JHuinapi/Proyecto-biodise-o-13/Talleres/Luis Gutiérrez Núñez.pdf

Luis Gutierrez Nuñez

Introduction to Sketching

September 21, 2025

Luis Gutierrez Nuñez

Introduction to Part Studios

September 21, 2025

Luis Gutierrez Nuñez

September 21, 2025

Multi-Part Part Studios

Luis Gutierrez Nuñez

September 21, 2025

Onshape Assemblies

Luis Gutierrez Nuñez

September 21, 2025

Detailed Drawings
