JHuinapi/Proyecto-biodise-o-13/Talleres/Taller 8/jonatan-huinapi-dbc9e937-857c-474c-9bc4-7a5a633f69ce-certificate.pdf

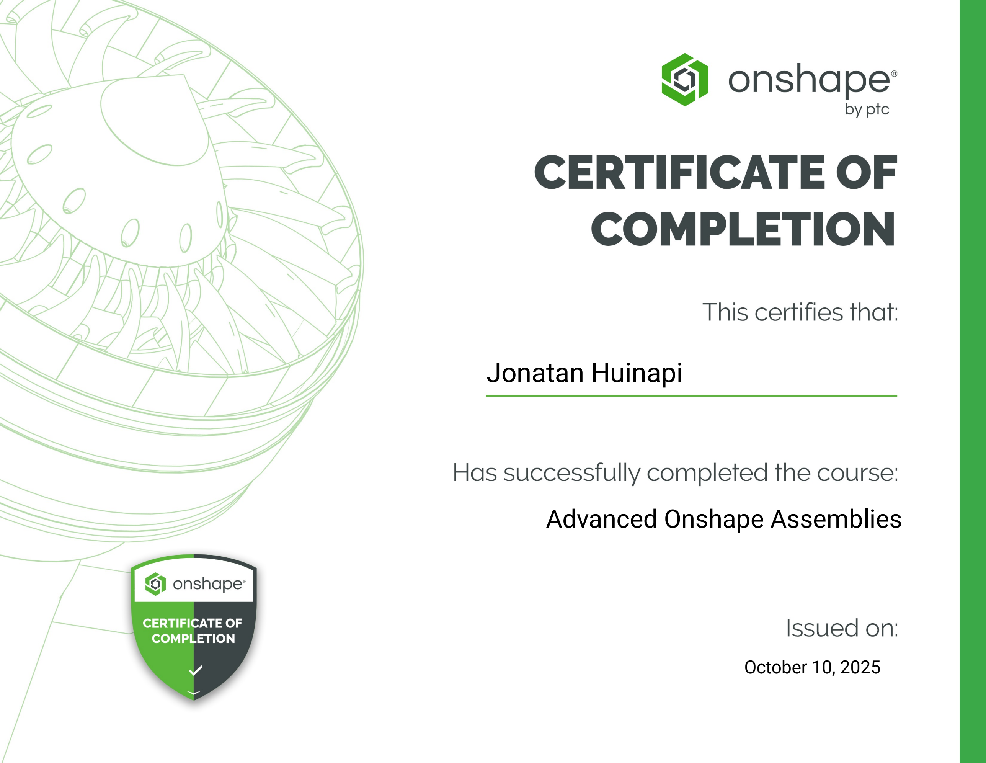
[picture p3: page 1]

Jonatan Huinapi

Advanced Onshape Assemblies

October 10, 2025
