JHuinapi/Proyecto-biodise-o-13/Documentacion/Entregables/Entregable N°8/Entregable N°8.pdf

## Entregable N°8

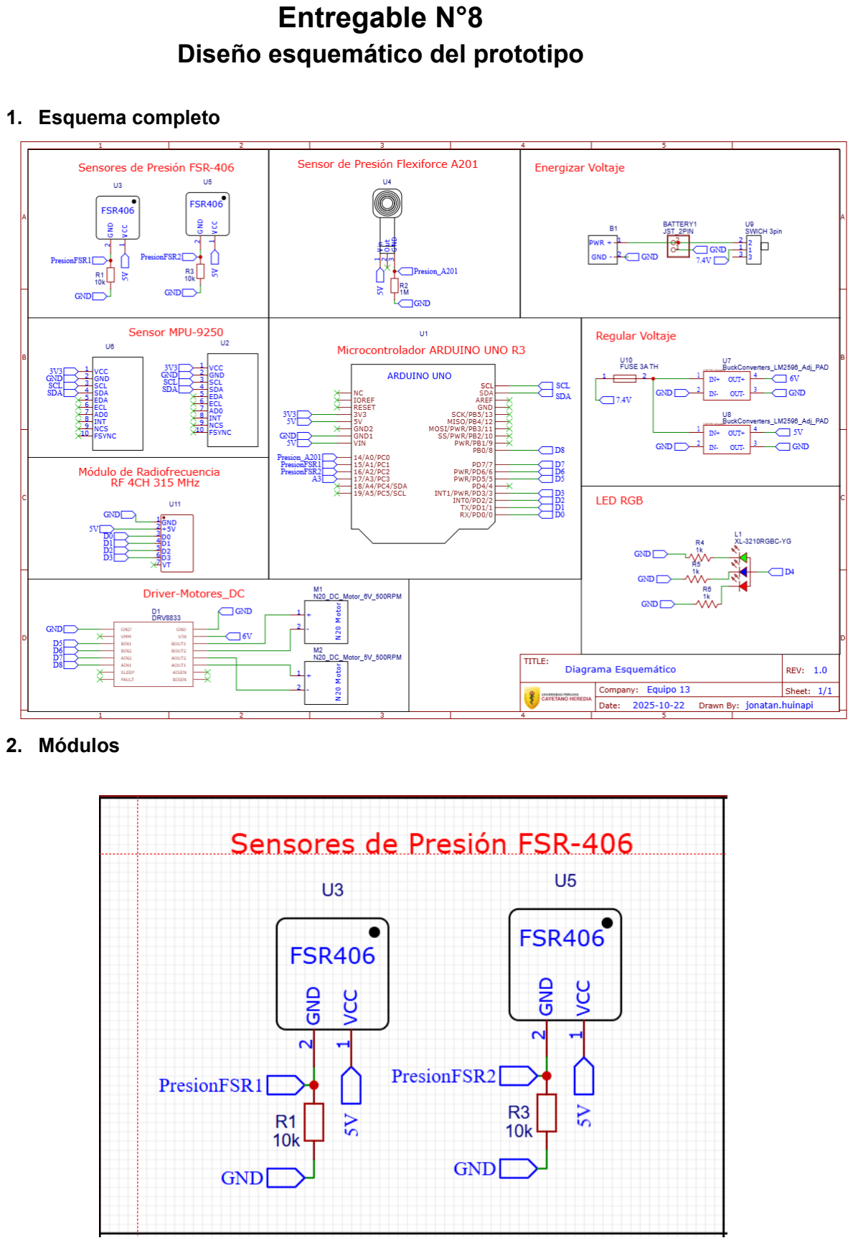
[picture p4: page 1]

### Diseño esquemático del prototipo

### 1. Esquema completo

### 2. Módulos

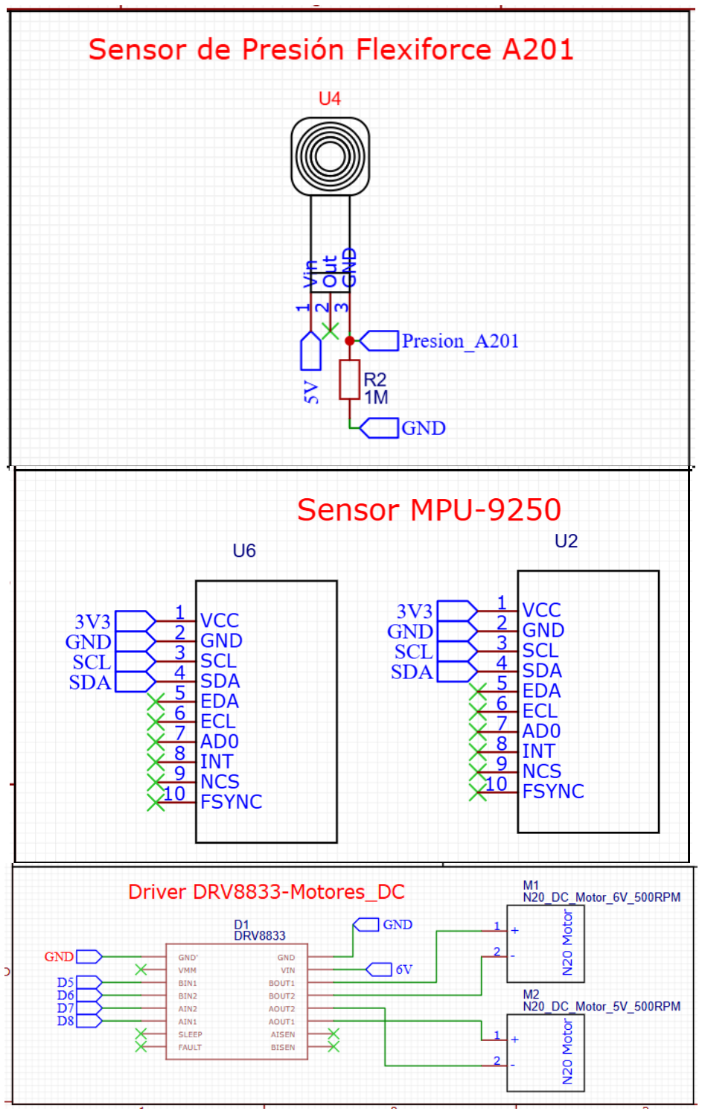
[picture p5: figure]
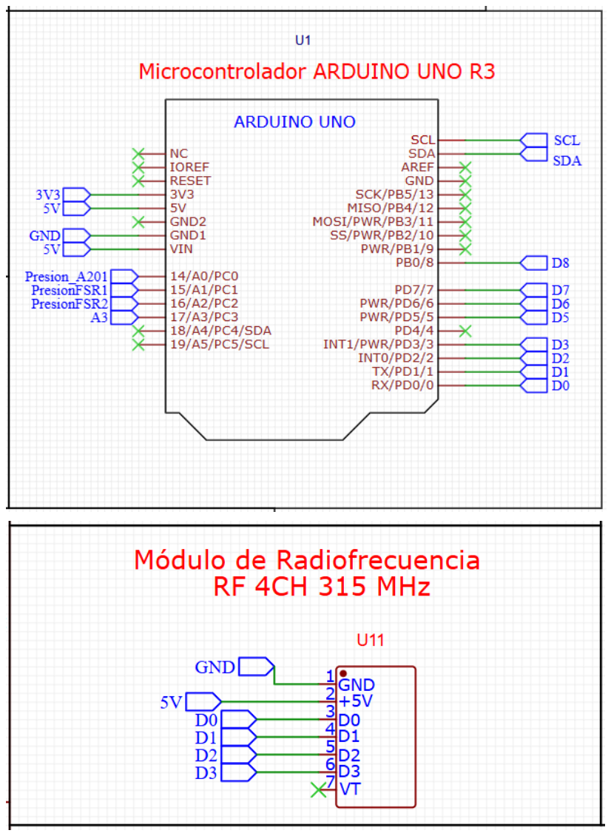
[picture p6: page 3]

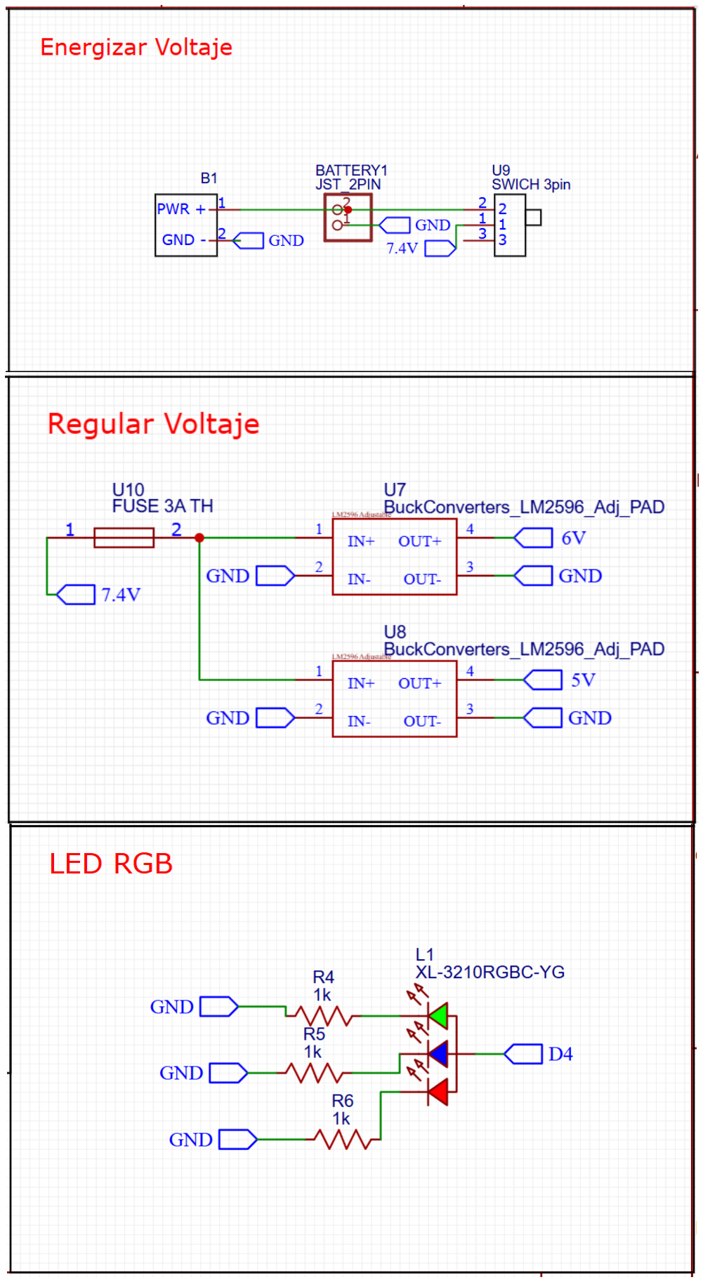
[picture p7: figure]

### Modelado 3D de los elementos que conforman su prototipo

Solución completa:
https://cad.onshape.com/documents/ef6f67d3207a1438bd075c8d/w/edfa028e2b72aa1350f10b2e/e/57896c7d0aa371fb77b32f57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 (https://cad.onshape.com/documents/ef6f67d3207a1438bd075c8d/w/edfa028e2b72aa1350f10b2e/e/57896c7d0aa371fb77b32f57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)

Componentes:

Arduino uno R3:

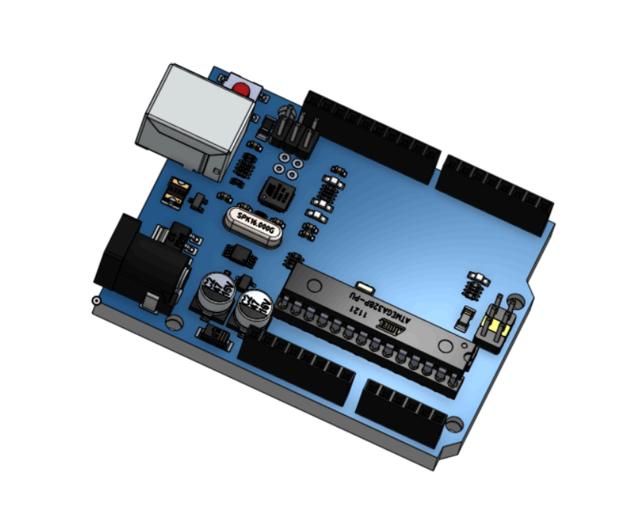
[picture p8: figure]

https://cad.onshape.com/documents/358e6ee0a7e545cdc13880cc/w/fb00525c6271bd48ed0 090b1 (https://cad.onshape.com/documents/358e6ee0a7e545cdc13880cc/w/fb00525c6271bd48ed0090b1)

LM 2596:

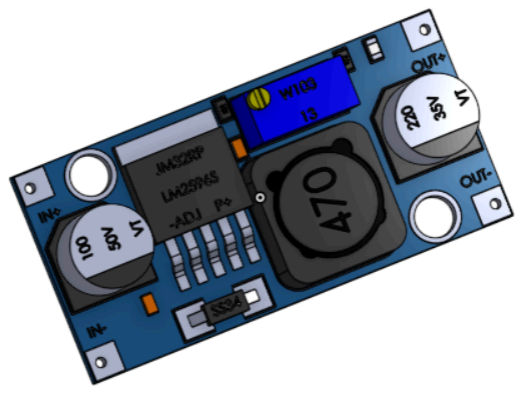
[picture p9: figure]

https://cad.onshape.com/documents/ed9dc76d7d66df3d99825e75/w/e64b5db6f0701456e918e3b2/e/382bef30aee71854fb0a7432 (https://cad.onshape.com/documents/ed9dc76d7d66df3d99825e75/w/e64b5db6f0701456e918e3b2/e/382bef30aee71854fb0a7432)

MPU 9250:

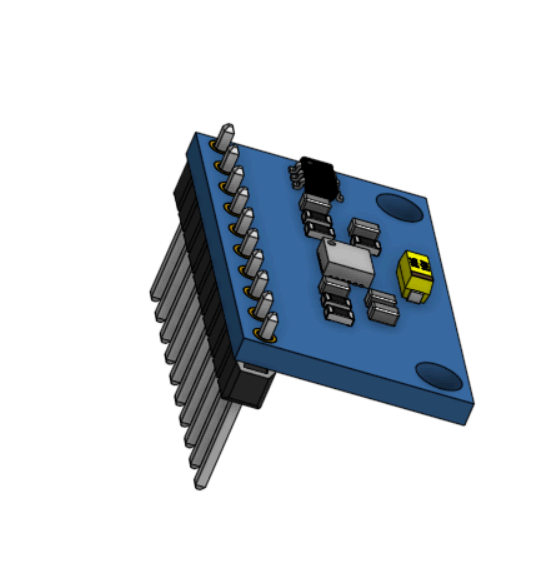
[picture p10: figure]

https://cad.onshape.com/documents/4e7dba8231ca7aadc371da44/w/675151ea96279376c8e2b919/e/e5ab18771fac6c1b0bbd111b (https://cad.onshape.com/documents/4e7dba8231ca7aadc371da44/w/675151ea96279376c8e2b919/e/e5ab18771fac6c1b0bbd111b)

Soporte largo:

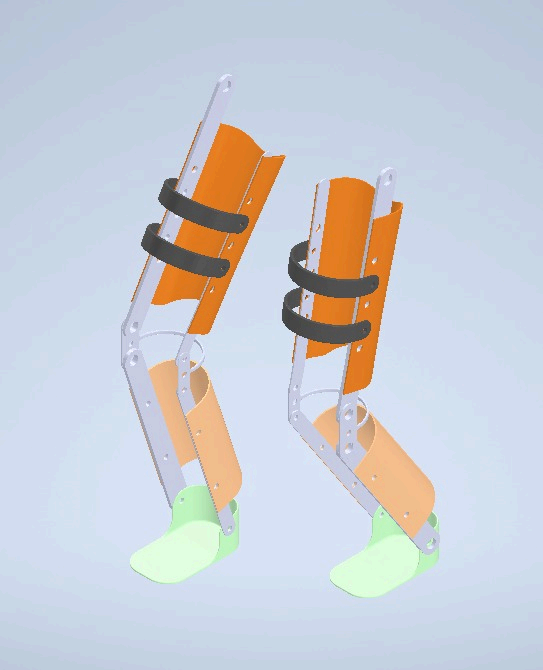
[picture p11: figure]

Ortesis para ambas piernas: https://cad.onshape.com/documents/b46cb4fec5818db489978633/w/90fc2fcc2cd690b41c06a4c6/e/ea05ce6ca1045edb00a44d7a (https://cad.onshape.com/documents/b46cb4fec5818db489978633/w/90fc2fcc2cd690b41c06a4c6/e/ea05ce6ca1045edb00a44d7a) https://cad.onshape.com/documents/85059d7c032bed2c8b1fd105/w/9daea419ead4c4d947 5dbce7 (https://cad.onshape.com/documents/85059d7c032bed2c8b1fd105/w/9daea419ead4c4d9475dbce7)

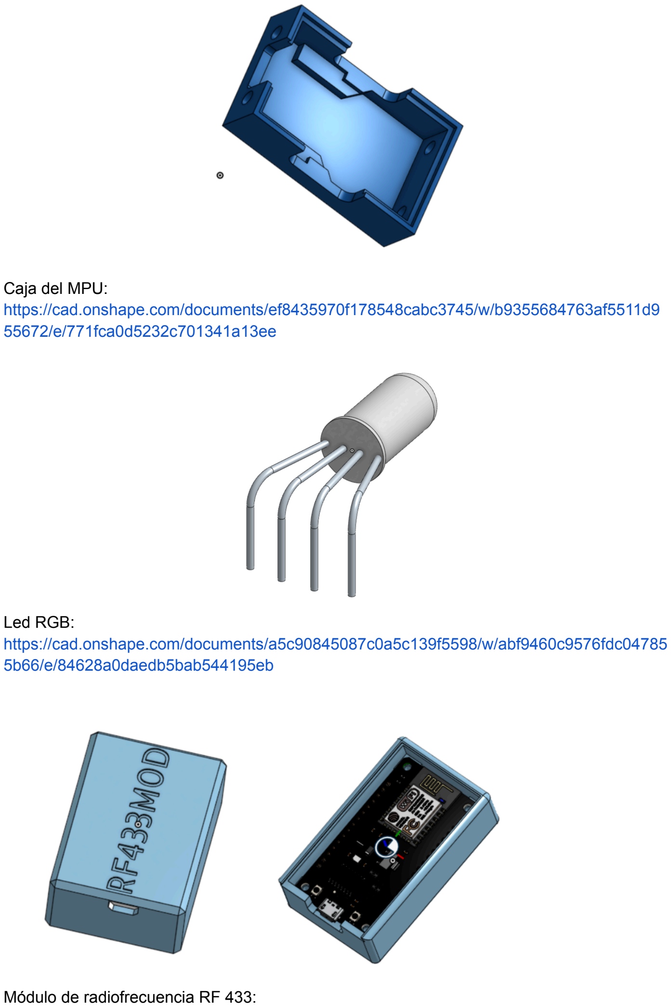
[picture p12: page 7]

Caja del MPU:
https://cad.onshape.com/documents/ef8435970f178548cabc3745/w/b9355684763af5511d955672/e/771fca0d5232c701341a13ee (https://cad.onshape.com/documents/ef8435970f178548cabc3745/w/b9355684763af5511d955672/e/771fca0d5232c701341a13ee)

Led RGB:
https://cad.onshape.com/documents/a5c90845087c0a5c139f5598/w/abf9460c9576fdc047855b66/e/84628a0daedb5bab544195eb (https://cad.onshape.com/documents/a5c90845087c0a5c139f5598/w/abf9460c9576fdc047855b66/e/84628a0daedb5bab544195eb)

Módulo de radiofrecuencia RF 433:

https://cad.onshape.com/documents/46bb01dfa372f61e05a1ae57/w/6816e948a11d4f39ffd87c3d/e/570a766bd7e573b261936c9a (https://cad.onshape.com/documents/46bb01dfa372f61e05a1ae57/w/6816e948a11d4f39ffd87c3d/e/570a766bd7e573b261936c9a) https://cad.onshape.com/documents/9d52821e4076e5f0773620d1/w/937a06b7c89ce3c964217ad0/e/10f29af23418c9318d54ea03 (https://cad.onshape.com/documents/9d52821e4076e5f0773620d1/w/937a06b7c89ce3c964217ad0/e/10f29af23418c9318d54ea03)

Parte del bastón canadiense:

Baston candiense:

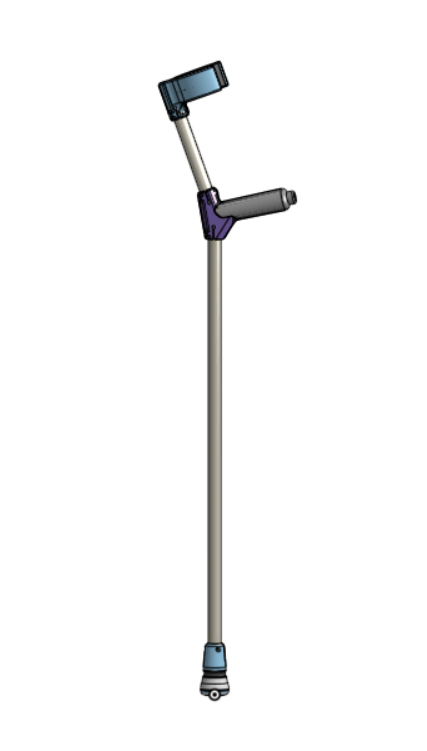
[picture p13: figure]

https://cad.onshape.com/documents/13cb7400194ab0a934fd1462/w/0d99d2ad3d134e4b89628924/e/30bec052ad2776449d337491 (https://cad.onshape.com/documents/13cb7400194ab0a934fd1462/w/0d99d2ad3d134e4b89628924/e/30bec052ad2776449d337491)

Soporte de boton:

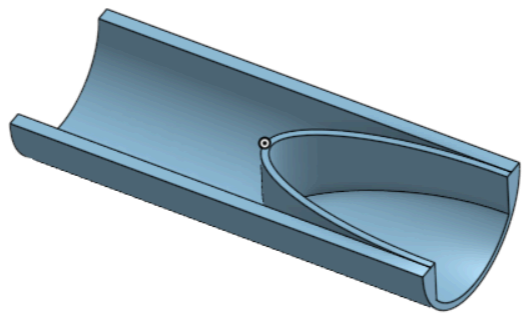
[picture p14: figure]

https://cad.onshape.com/documents/9404f07777c095b4e53f477f/w/989ea8cd8fd72e54b5d60ba9/e/30a6f88c9f77ebc46748e171 (https://cad.onshape.com/documents/9404f07777c095b4e53f477f/w/989ea8cd8fd72e54b5d60ba9/e/30a6f88c9f77ebc46748e171)

Bateria Lipo:

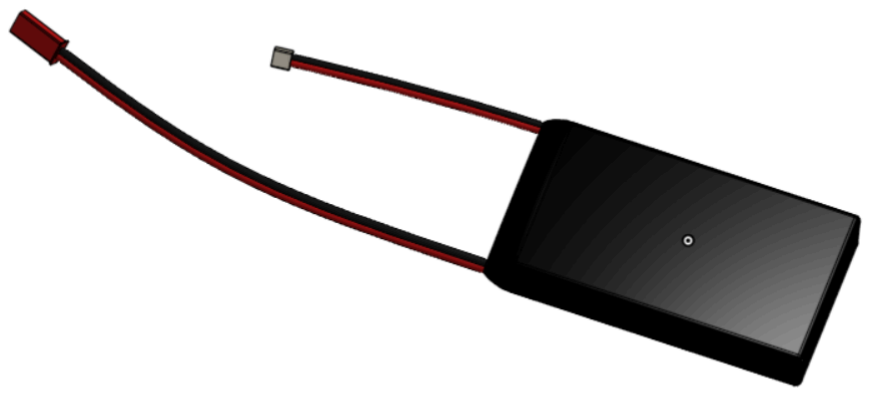
[picture p15: figure]

https://cad.onshape.com/documents/a1dde294c337bbebe96d0394/w/6668284372e06987ff7d8810/e/77b050f4c0bf37e111e226cb (https://cad.onshape.com/documents/a1dde294c337bbebe96d0394/w/6668284372e06987ff7d8810/e/77b050f4c0bf37e111e226cb)

Partes de la plantilla:

Plantilla:

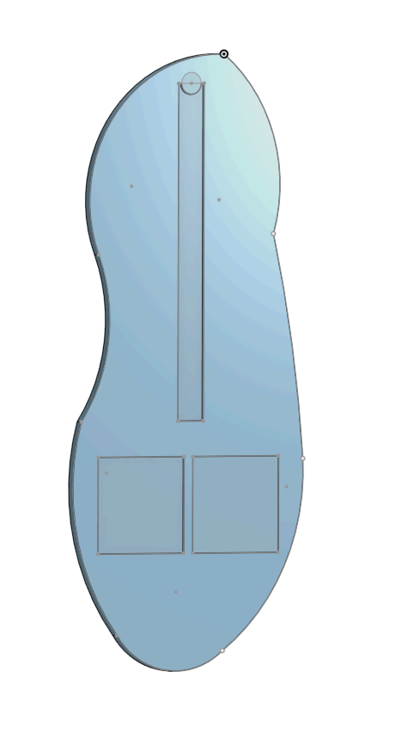
[picture p16: figure]

https://cad.onshape.com/documents/90b00f3962dbd41c6fcc8b45/w/5ce1db6625fad7db0d8d7604/e/39d914baed3868cf32210c26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 (https://cad.onshape.com/documents/90b00f3962dbd41c6fcc8b45/w/5ce1db6625fad7db0d8d7604/e/39d914baed3868cf32210c26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)

Sensores de fuerza:

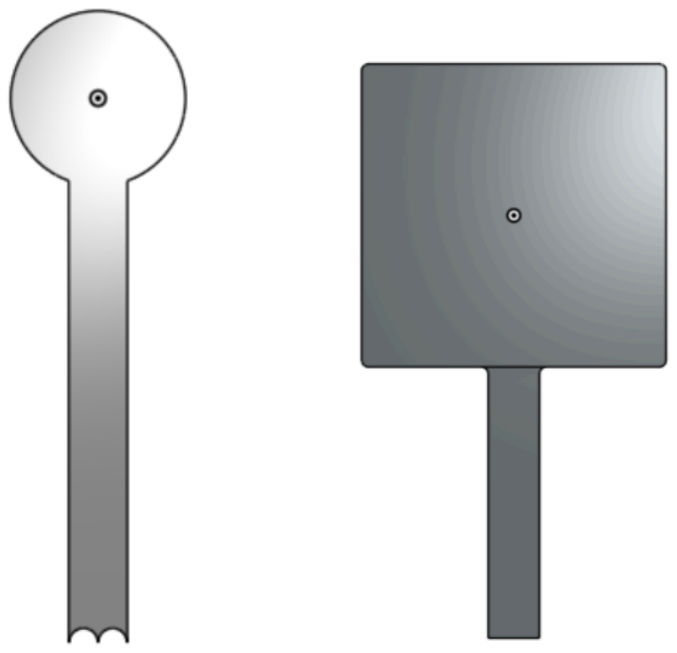
[picture p17: figure]

https://cad.onshape.com/documents/090143753a29e05ed30aaa47/w/a6cd4efa5bea32224642f22c/e/10581780c01f5d9f3ce7b4fe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 (https://cad.onshape.com/documents/090143753a29e05ed30aaa47/w/a6cd4efa5bea32224642f22c/e/10581780c01f5d9f3ce7b4fe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) https://cad.onshape.com/documents/b9766196f22d7fde754003f2/w/f4f8ca196eb82ef86cc7a587/e/8ac04a6db70dde7c7fe50fd8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 (https://cad.onshape.com/documents/b9766196f22d7fde754003f2/w/f4f8ca196eb82ef86cc7a587/e/8ac04a6db70dde7c7fe50fd8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)

Partes del sistema de trabe y destrabe:

Micromotor N20:

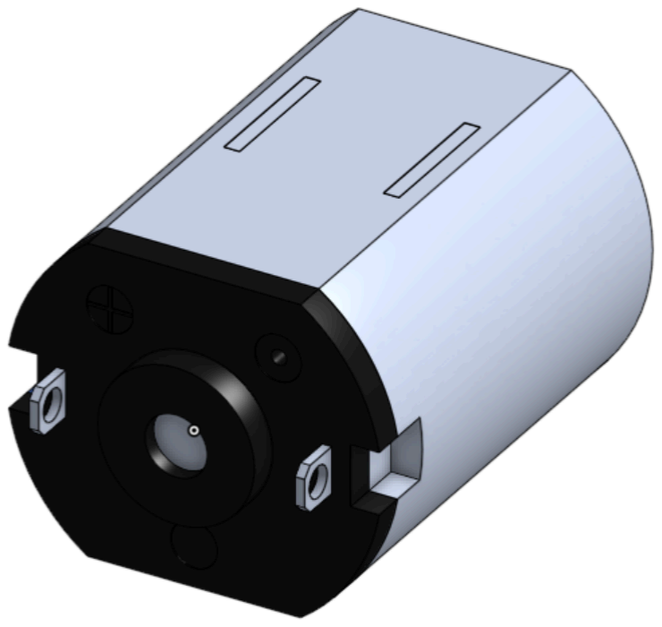
[picture p18: figure]

https://cad.onshape.com/documents/a79e828ba8c9972a8f85b02b/w/044c2e34d4fcb483626a1345/e/9966f7c9ecc495e53f5c1f4e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 (https://cad.onshape.com/documents/a79e828ba8c9972a8f85b02b/w/044c2e34d4fcb483626a1345/e/9966f7c9ecc495e53f5c1f4e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)

Poleas:

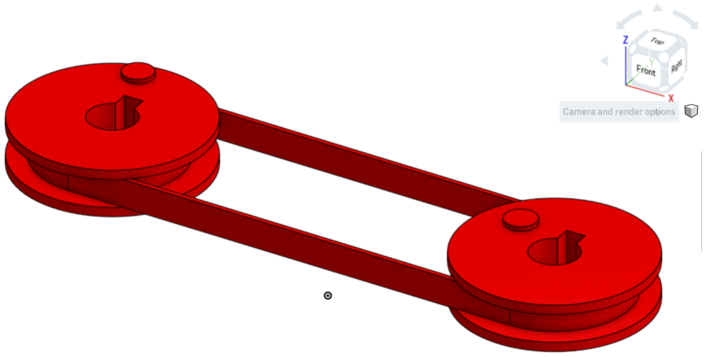
[picture p19: figure]

https://cad.onshape.com/documents/feb36c91eed124813346efae/w/b8817322451c90e2da5b96ee/e/90c357cbd19b11150c3f9f70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 (https://cad.onshape.com/documents/feb36c91eed124813346efae/w/b8817322451c90e2da5b96ee/e/90c357cbd19b11150c3f9f70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)

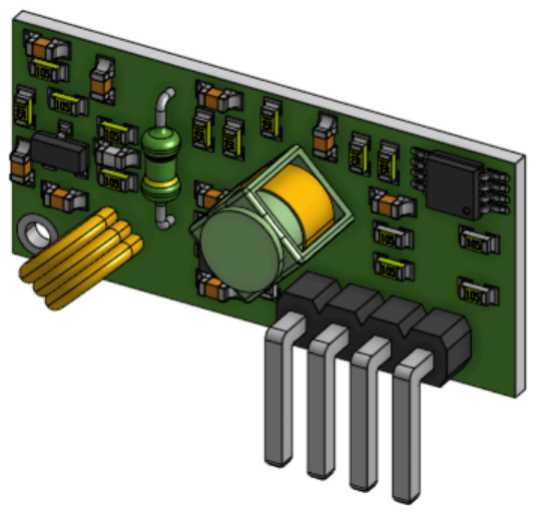
[picture p20: figure]

01COM RX RF433 Receiver:
https://cad.onshape.com/documents/082a6ee97619ae0f739f296e/w/c65dcdce71237949594d5020/e/2d733671bed38224296ad423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 2 (https://cad.onshape.com/documents/082a6ee97619ae0f739f296e/w/c65dcdce71237949594d5020/e/2d733671bed38224296ad423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)

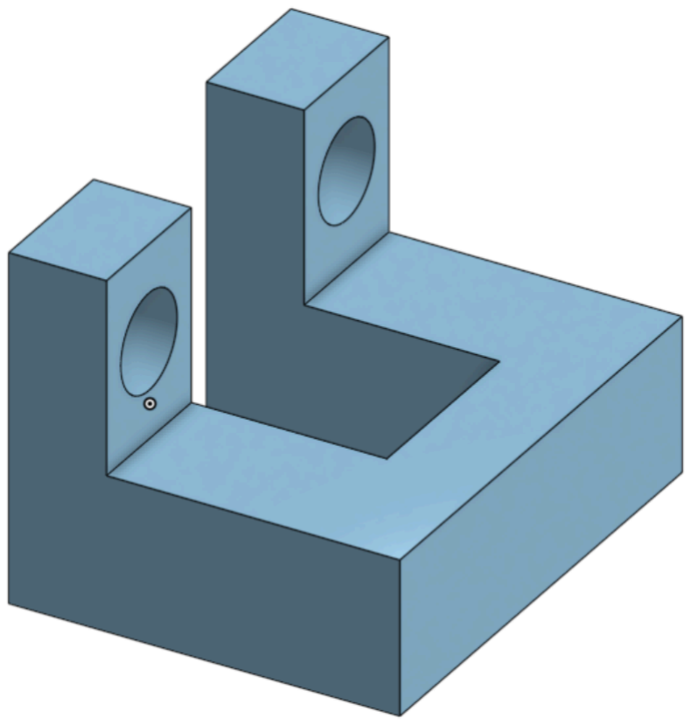
[picture p21: figure]

Gancho para poleas:
https://cad.onshape.com/documents/0540d481ef109f192a8d81a9/w/1a57b690e35bc69c4da5a976/e/339e8275e2c3247a0a6f577b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 (https://cad.onshape.com/documents/0540d481ef109f192a8d81a9/w/1a57b690e35bc69c4da5a976/e/339e8275e2c3247a0a6f577b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)

Pieza para trabar:

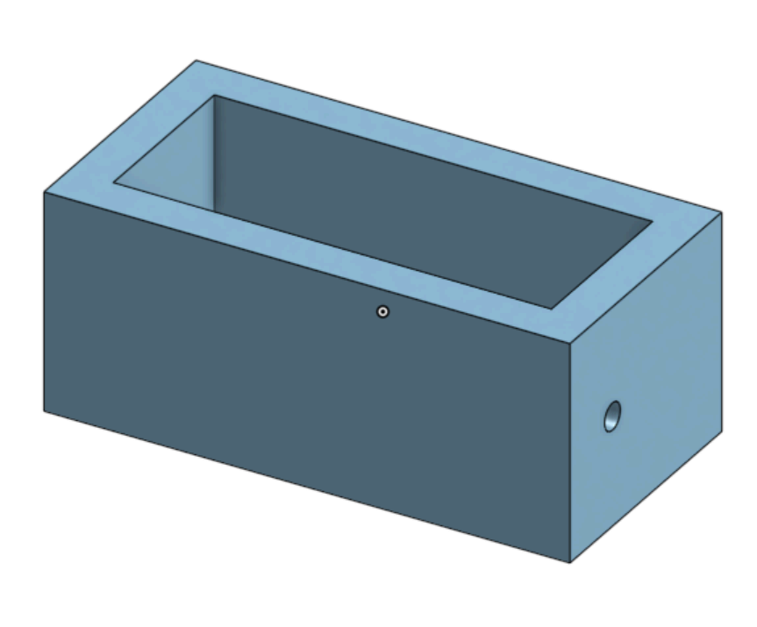
[picture p22: figure]

https://cad.onshape.com/documents/76d2d7c239bdc8f8fa00e4ad/w/cebd49e91c2a0bf198104d18/e/7dd4c7551fcfe9fa7b047bc8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 (https://cad.onshape.com/documents/76d2d7c239bdc8f8fa00e4ad/w/cebd49e91c2a0bf198104d18/e/7dd4c7551fcfe9fa7b047bc8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)
