JHuinapi/Proyecto-biodise-o-13/Documentacion/Hito №2/Hito 2_FdB_2025_2.pdf

## Indicaciones

- Este template es un esquema base para la construcción de su Elevator Pitch en base a los entregables del curso.
- Se recomienda hacer una presentación con alto contenido visual, enfocada en presentar ideas centrales en un Pitch de 7 minutos.
- El diseño estético de la carátula y de las demás diapositivas queda a criterio del alumno. El orden y contenido indicado en cada slide es obligatorio.
- Se recomienda ceñirse al número de slides del template, para utilizar aproximadamente 1 min/diapositiva y culminar en el tiempo asignado. Sean precisos y claros en su discurso.
- El slide para la demo está fuera de los 7 min y puede durar 2:00 min máx. Los slides extra son para información de soporte durante las preguntas de los asesores respecto a los retos y limitaciones de sus prototipos.
- Asistir con vestimenta formal para la presentación del Hito N° 2.

¡Éxitos en su presentación!

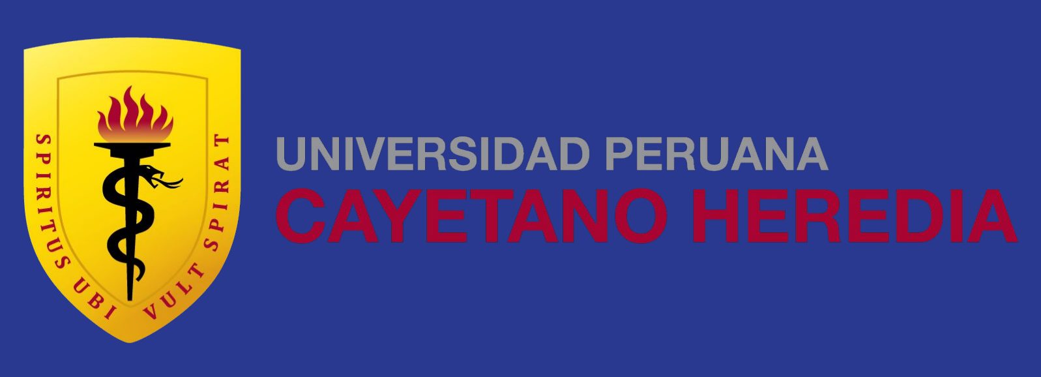
[picture p49: figure]

# KAFO-Pulley Assist

Integrantes: Grupo 13

- Gutierrez Nuñez, Luis Antonio. Rol: Técnico en electrónica y programación
- Hernandez Jeronimo, Xavier Alexis. Rol: Responsable de metodología y documentación
- Huiñapi Huaman, Jonatan Esteban. Rol: Líder del proyecto y especialista en electrónica y programación
- Mamani Casas, Alexandra Milagros. Rol: Diseñadora 3D principal
- Morocho Bustamante, Mariam Michelle. Rol: Diseñadora 3D y encargada de manufactura aditiva
- Murillo Sedano, Ricardo Sebastián. Rol: Apoyo metodológico y encargado de impresión 3D

## Problemática

- “ Control Method for a powered knee ankle foot orthosis”
- Número de patente: W02022231566
- Trainer in a pocket - proof-of-concept of mobile, real-time, foot kinematics feedback for gait pattern normalization in individuals after stroke, incomplete spinal cord injury and elderly patients
- Design, Control, and Pilot Study of a Lightweight and Modular Robotic Exoskeleton for Walking Assistance After Spinal Cord Injury

El paciente presenta una zona de preservación parcial (ZPP) en la rodilla, permitiendo su flexión. Además de la falta de sensibilidad en la parte inferior del cuerpo desde el nivel T10.

Referencias con mayor relevancia en el desarrollo del proyecto:

## Solución

Ortesis KAFO con bloqueo controlado mediante sistema de poleas motorizado.

Funcionamiento en tres pasos del prototipo:

1. El usuario presiona un botón para bloquear o desbloquear la rodilla.
2. Un motor acciona las poleas que mueven el mecanismo de drop lock, además se registran datos de posicionamiento del pie.
3. El sistema fija o libera la articulación según la orden enviada y brinda una retroalimentación de datos en forma de guía visual.

## Tracción

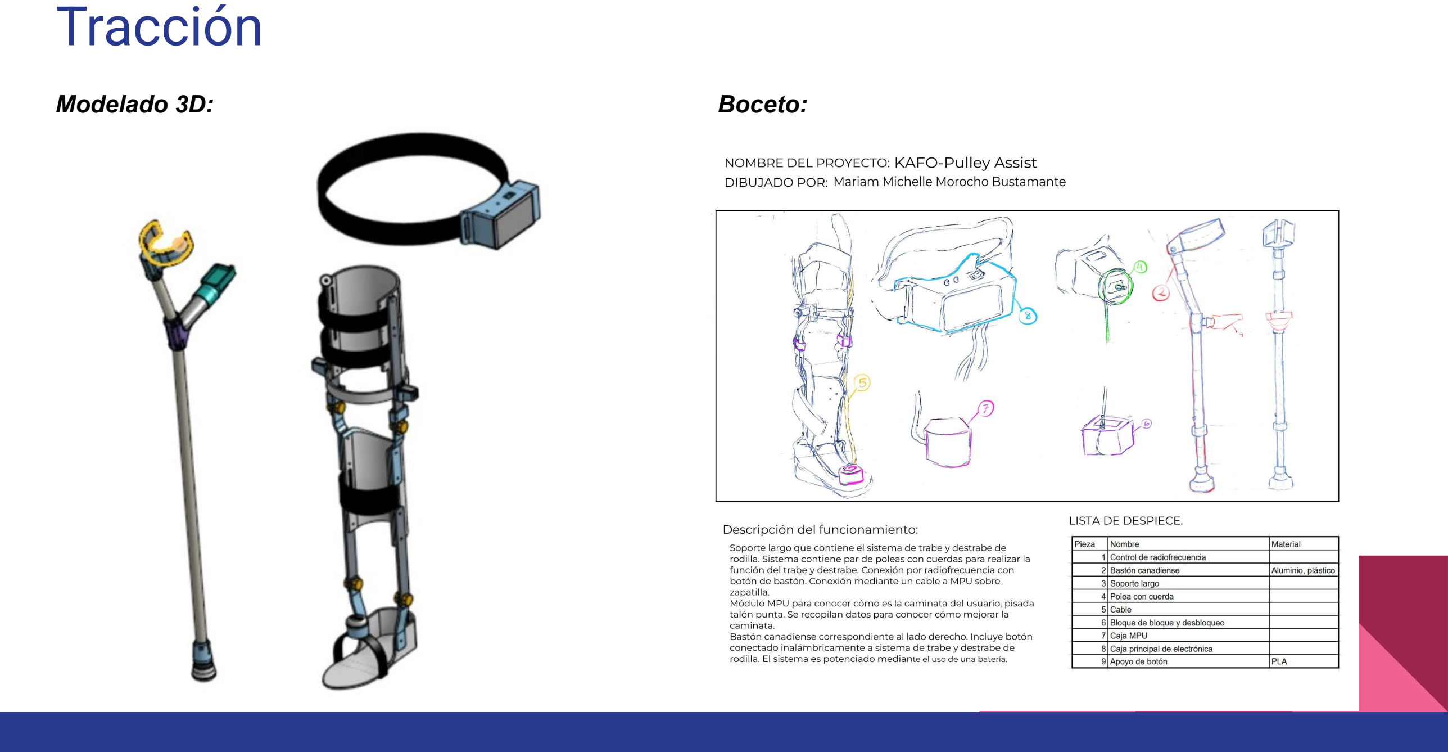
[picture p50: page 5]

Modelado 3D: | Boceto:

## Tracción

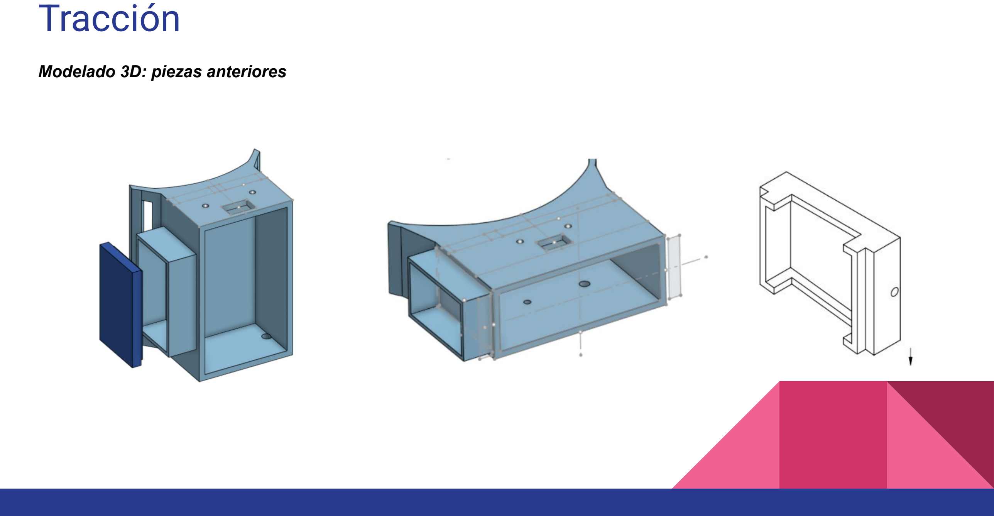
[picture p51: page 6]

Modelado 3D: piezas anteriores

## Tracción

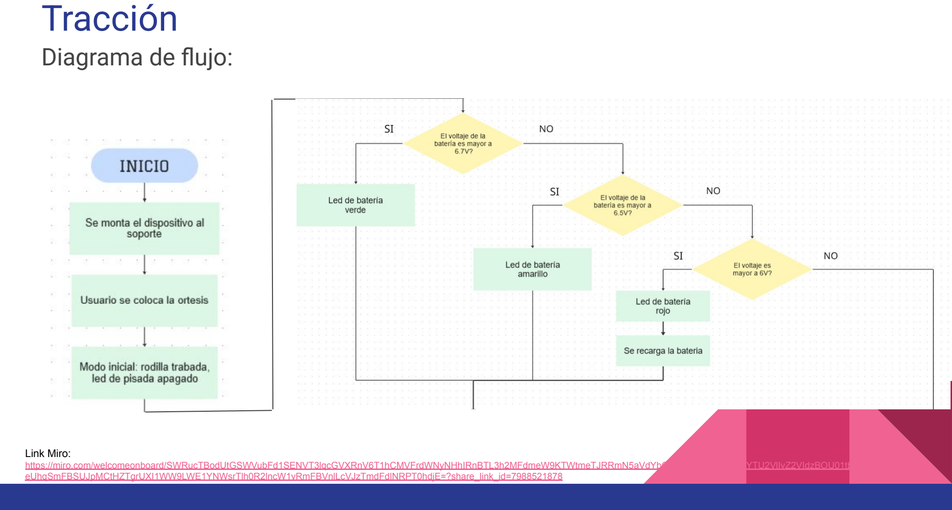
[picture p52: page 7]

Diagrama de flujo:

Link Miro:
https://miro.com/welcomeonboard/SWRucTBodUtGSWVubFd1SENVT3lqcGVXRnV6T1hCMVFrdWNyNHhIRnBTL3h2MFdmeW9KTWtmeTJRRmN5aVdYbGxjRTZJUUhTZUFPYTU2VlIvZ2VIdzBOU01tbndGR1pOQmM4e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 (https://miro.com/welcomeonboard/SWRucTBodUtGSWVubFd1SENVT3lqcGVXRnV6T1hCMVFrdWNyNHhIRnBTL3h2MFdmeW9KTWtmeTJRRmN5aVdYbGxjRTZJUUhTZUFPYTU2VlIvZ2VIdzBOU01tbndGR1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)

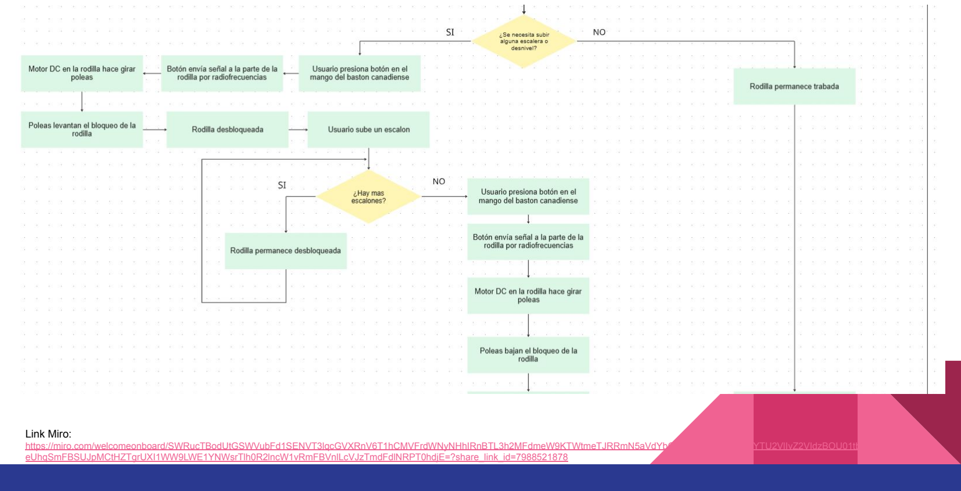
[picture p53: page 8]

Link Miro:
https://miro.com/welcomeonboard/SWRucTBodUtGSWVubFd1SENVT3lqcGVXRnV6T1hCMVFrdWNyNHhIRnBTL3h2MFdmeW9KTWtmeTJRRmN5aVdYbGxjRTZJUUhTZUFPYTU2VlIvZ2VIdzBOU01tbndGR1pOQmM4e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 (https://miro.com/welcomeonboard/SWRucTBodUtGSWVubFd1SENVT3lqcGVXRnV6T1hCMVFrdWNyNHhIRnBTL3h2MFdmeW9KTWtmeTJRRmN5aVdYbGxjRTZJUUhTZUFPYTU2VlIvZ2VIdzBOU01tbndGR1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)

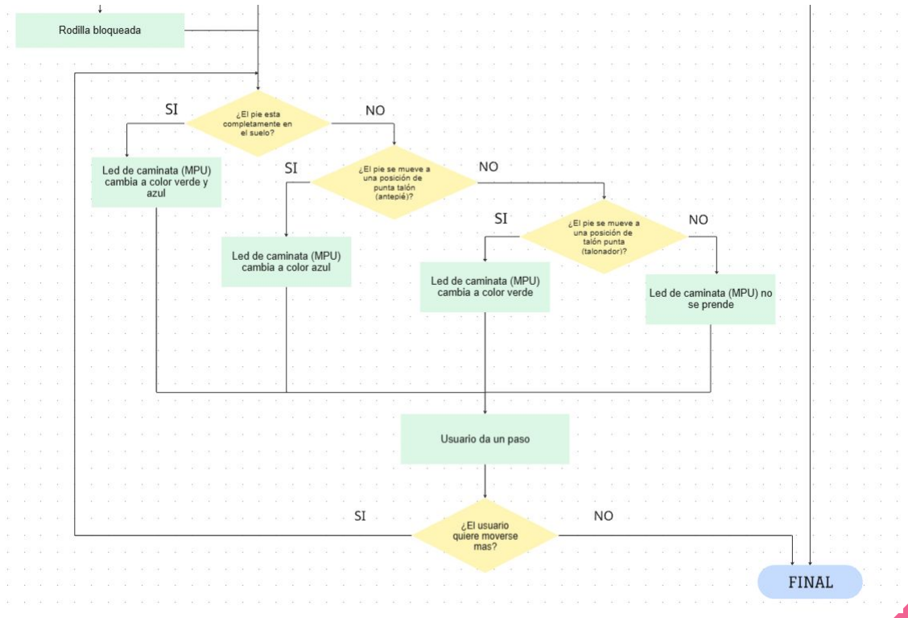
[picture p54: figure]

Link Miro:
https://miro.com/welcomeonboard/SWRucTBodUtGSWVubFd1SENVT3lqcGVXRnV6T1hCMVFrdWNyNHhIRnBTL3h2MFdmeW9KTWtmeTJRRmN5aVdYbGxjRTZJUUhTZUFPYTU2VlIvZ2VIdzBOU01tbndGR1pOQmM4e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 (https://miro.com/welcomeonboard/SWRucTBodUtGSWVubFd1SENVT3lqcGVXRnV6T1hCMVFrdWNyNHhIRnBTL3h2MFdmeW9KTWtmeTJRRmN5aVdYbGxjRTZJUUhTZUFPYTU2VlIvZ2VIdzBOU01tbndGR1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)

## Tracción

Entregable: Diagrama Esquemático del prototipo electrónico

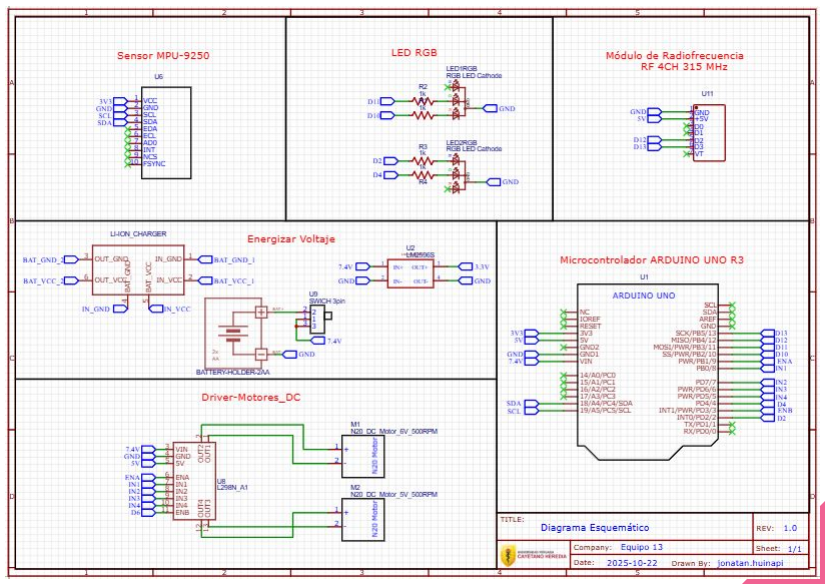
[picture p55: figure]

## Tracción

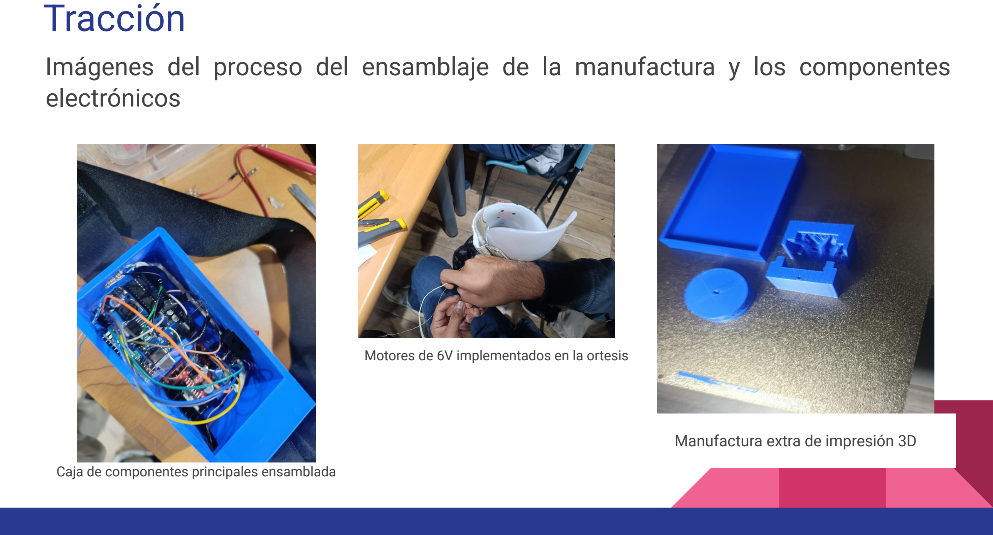
[picture p56: page 11]

Imágenes del proceso del ensamblaje de la manufactura y los componentes electrónicos

Caja de componentes principales ensamblada

Motores de 6V implementados en la ortesis

Manufactura extra de impresión 3D

## Tracción

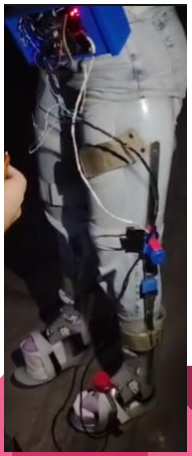
[picture p57: figure]

Resultados software: El dispositivo retroalimenta datos del estado de batería, además del correcto posicionamiento del pie y el usuario tiene acceso a los cambios de modo y encendido/apagado del sistema en general.

Resultados hardware: El dispositivo permite alternar entre modos sin apoyo de terceros, los componentes son acoplados de forma no invasiva a la ortesis y usuario, los elementos adicionales pesan menos de 600 gramos y no se presentan inconvenientes en la comodidad del usuario.

## Tracción: Demo

Videos del prototipo de baja fidelidad en ambas partes principales del proyecto

Funcionamiento mecánico | Funcionamiento electrónico

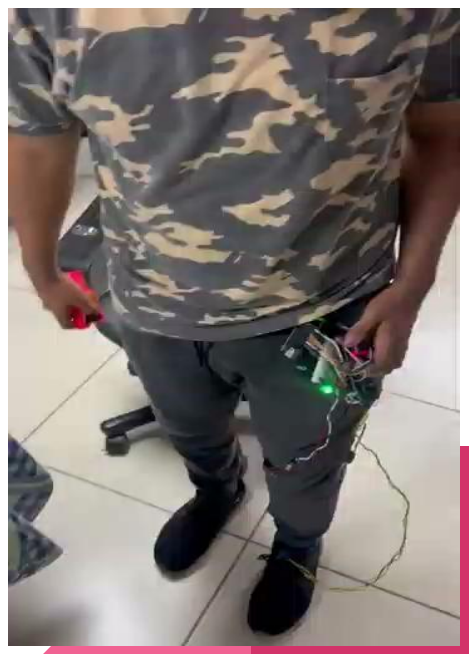
[picture p58: figure]

## Slide extra: Limitaciones

Se presentaron limitaciones externas tales como el cambio de material base el cual se cambió la forma y posicionamiento del soporte empleado en la ortesis. Para mitigar se tuvo que redimensionar el diseño entero.

Hubo limitaciones de tiempo en el trabajo debido al replanteamiento de idea por el sistema de reeducación implementado, además de el cambio de un modo de sistema automático a uno netamente semiautomático. Para mitigar se tuvo que mantener el mismo esquema de funciones y planteamiento de distribución de componentes cambiando algunos parámetros, pero manteniendo la idea general.

## Slide extra: Pruebas y testeos

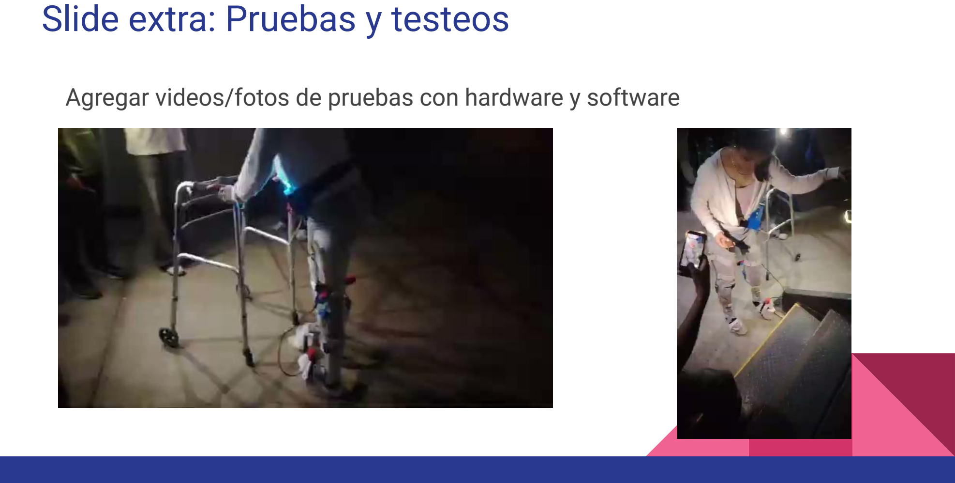
[picture p59: page 15]

Agregar videos/fotos de pruebas con hardware y software
