JHuinapi/Proyecto-biodise-o-13/Talleres/Jonatan Esteban Huiñapi Huaman/jonatan-huinapi-certificate-Introduction to sketching.pdf

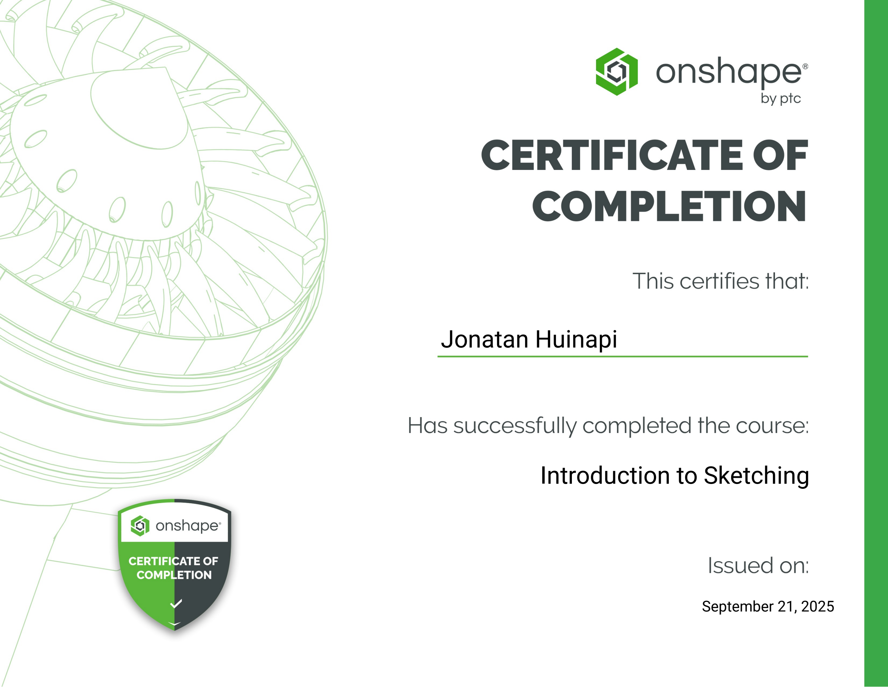
[picture p74: page 1]

Jonatan Huinapi

Introduction to Sketching

September 21, 2025
