JHuinapi/Proyecto-biodise-o-13/Talleres/Jonatan Esteban Huiñapi Huaman/jonatan-huinapi-Detailed Drawing-certificate.pdf

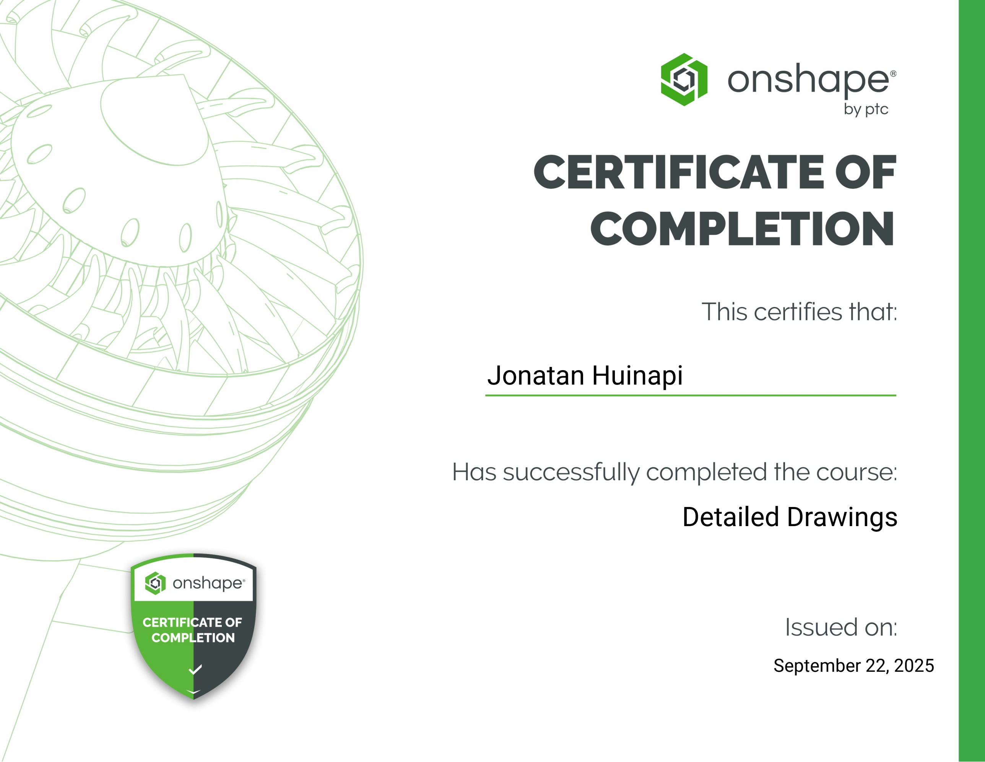
[picture p75: page 1]

Jonatan Huinapi

September 22, 2025

Detailed Drawings
