JHuinapi/Proyecto-biodise-o-13/Talleres/Jonatan Esteban Huiñapi Huaman/jonatan-huinapi-Introduction to part studios certificate.pdf

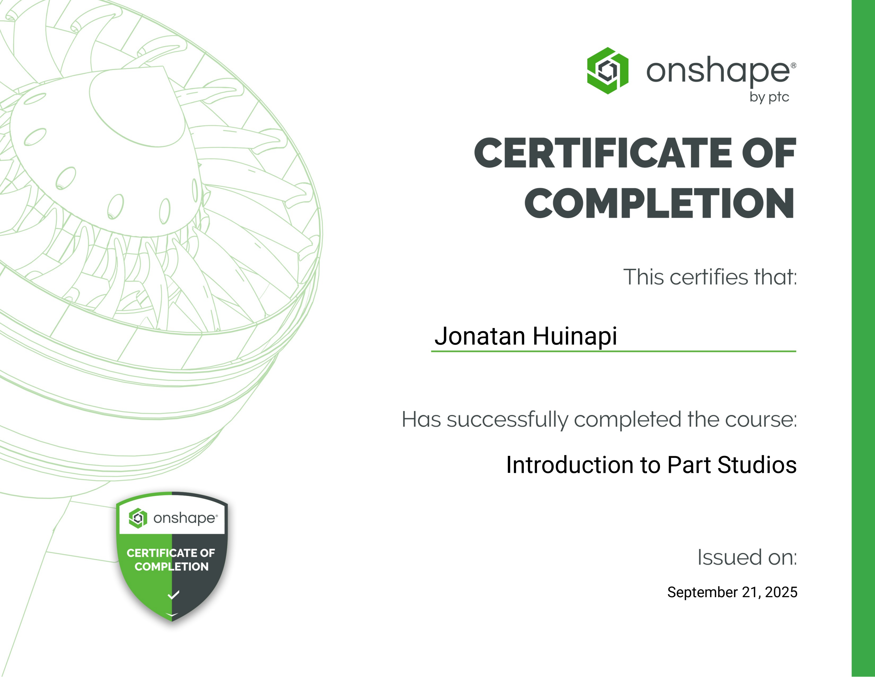
[picture p76: page 1]

Jonatan Huinapi

Introduction to Part Studios

September 21, 2025
