JHuinapi/Proyecto-biodise-o-13/Talleres/Jonatan Esteban Huiñapi Huaman/jonatan-huinapi-Multi-part Part studios-certificate.pdf

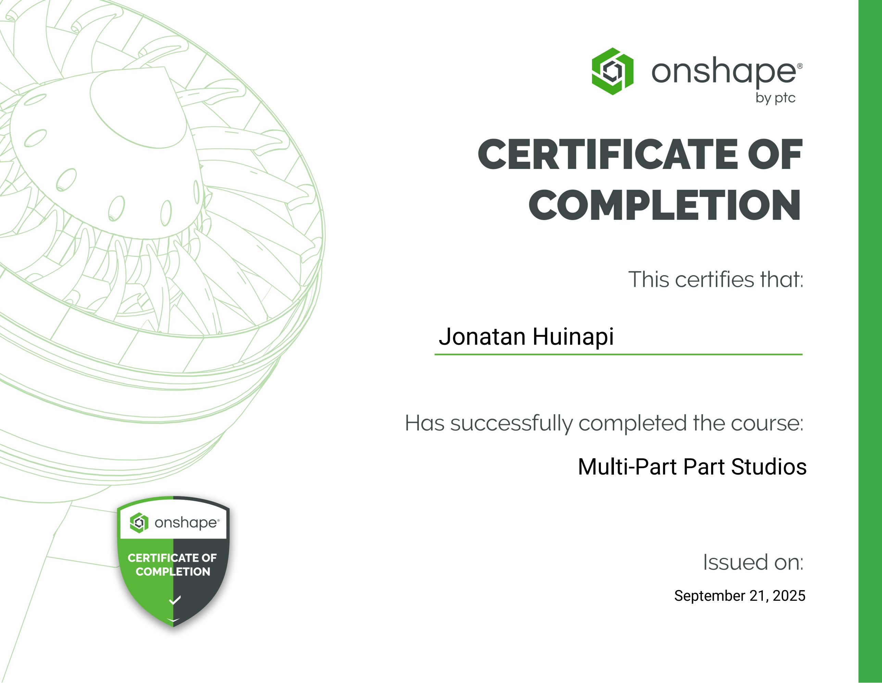
[picture p77: page 1]

Jonatan Huinapi

September 21, 2025

Multi-Part Part Studios
