JHuinapi/Proyecto-biodise-o-13/Talleres/Hernandez Jeronimo Xavier Alexis/Detailed Drawings.pdf

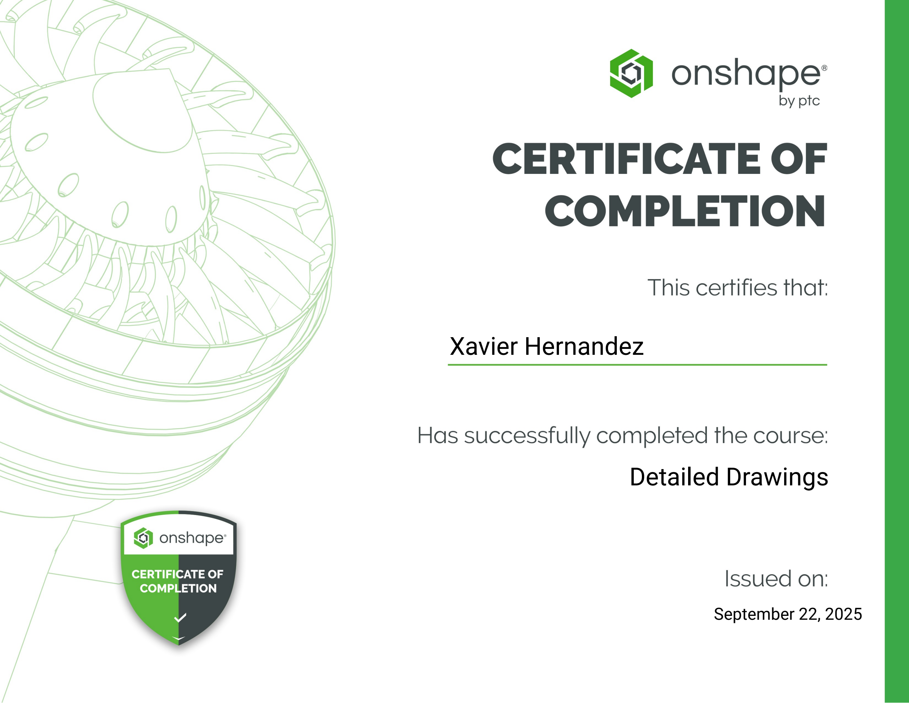
[picture p78: page 1]

Xavier Hernandez

September 22, 2025

Detailed Drawings
