JHuinapi/Proyecto-biodise-o-13/Talleres/Hernandez Jeronimo Xavier Alexis/Introduction to Part Studios.pdf

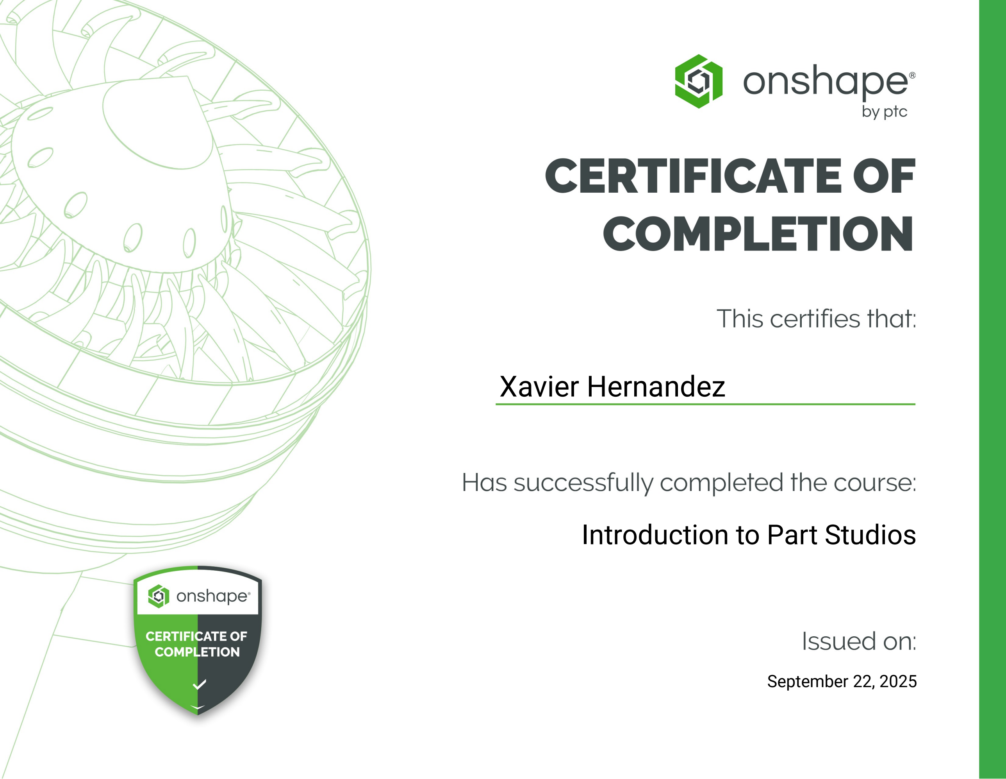
[picture p79: page 1]

Xavier Hernandez

Introduction to Part Studios

September 22, 2025
