JHuinapi/Proyecto-biodise-o-13/Talleres/Hernandez Jeronimo Xavier Alexis/Multi-Part Part Studios.pdf

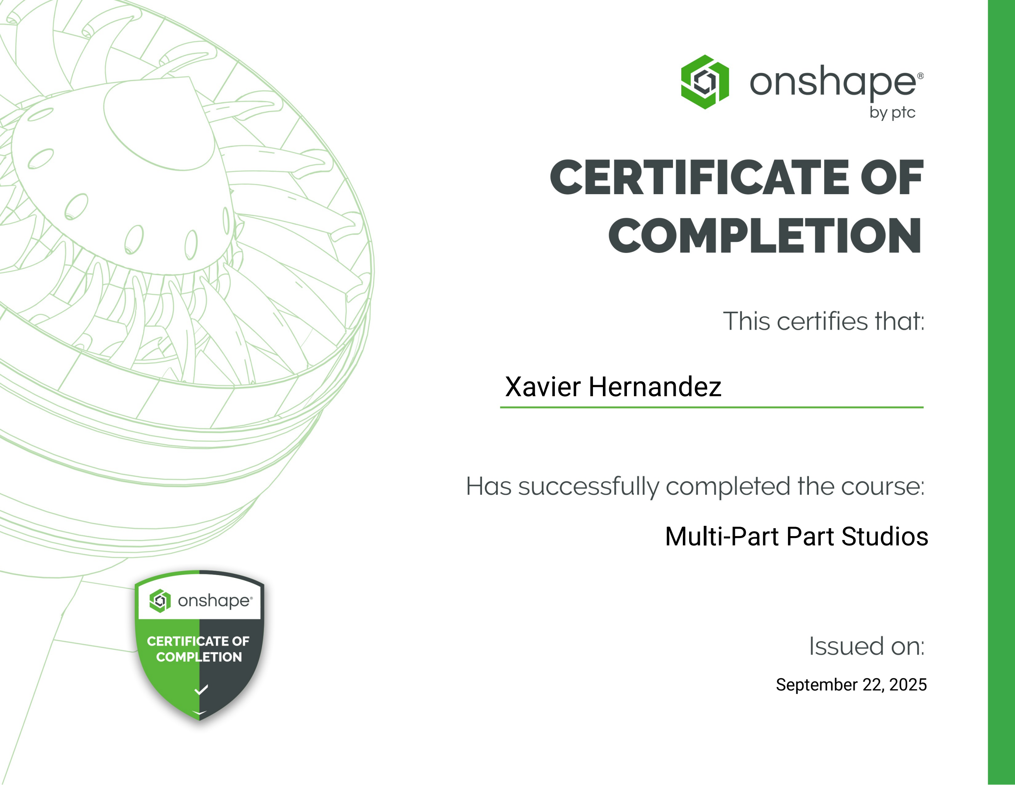
[picture p80: page 1]

Xavier Hernandez

September 22, 2025

Multi-Part Part Studios
