JHuinapi/Proyecto-biodise-o-13/Talleres/Hernandez Jeronimo Xavier Alexis/Introduction to Sketching.pdf

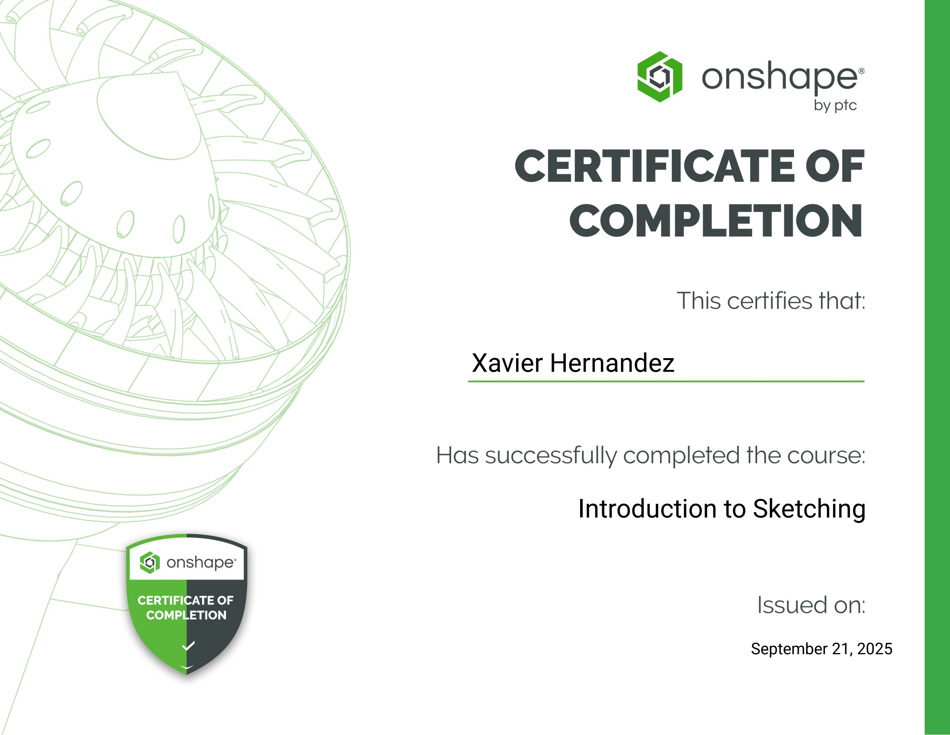
[picture p81: page 1]

Xavier Hernandez

Introduction to Sketching

September 21, 2025
