JHuinapi/Proyecto-biodise-o-13/Talleres/Morocho Bustamante, Mariam Michelle/MariamMorochoBustamante_DetailedDrawings.pdf

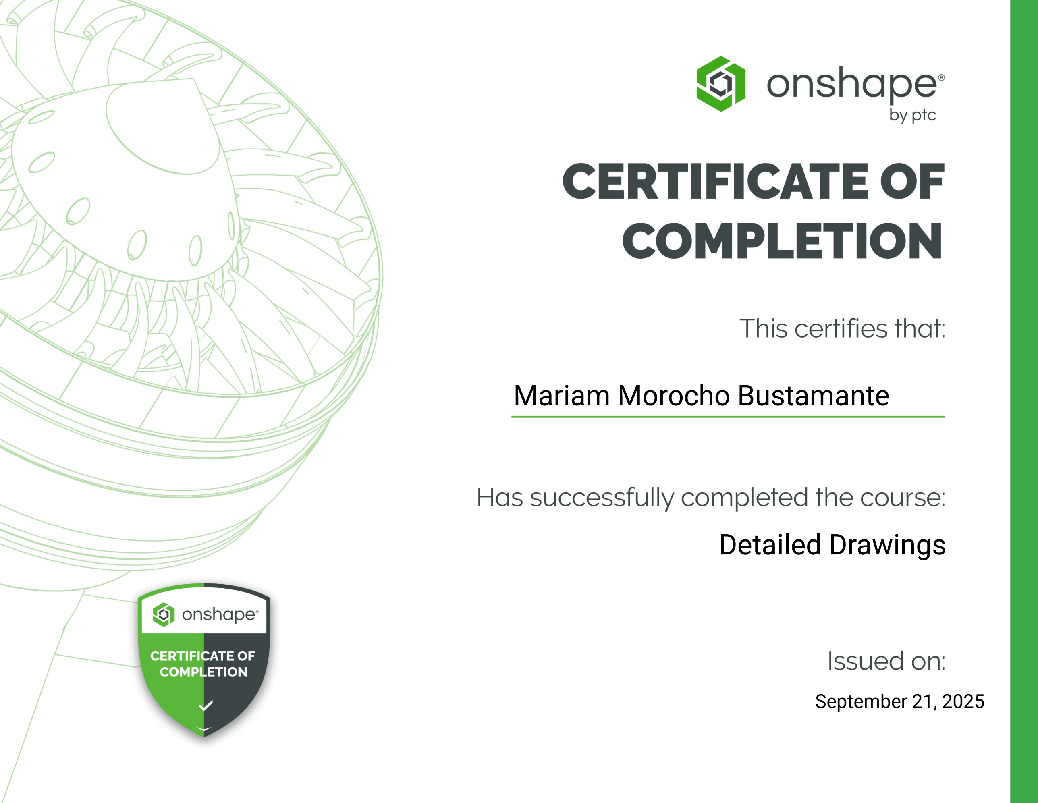
[picture p82: page 1]

Mariam Morocho Bustamante

September 21, 2025

Detailed Drawings
