JHuinapi/Proyecto-biodise-o-13/Talleres/Morocho Bustamante, Mariam Michelle/MariamMorochoBustamante_IntroductionToPartStudio.pdf

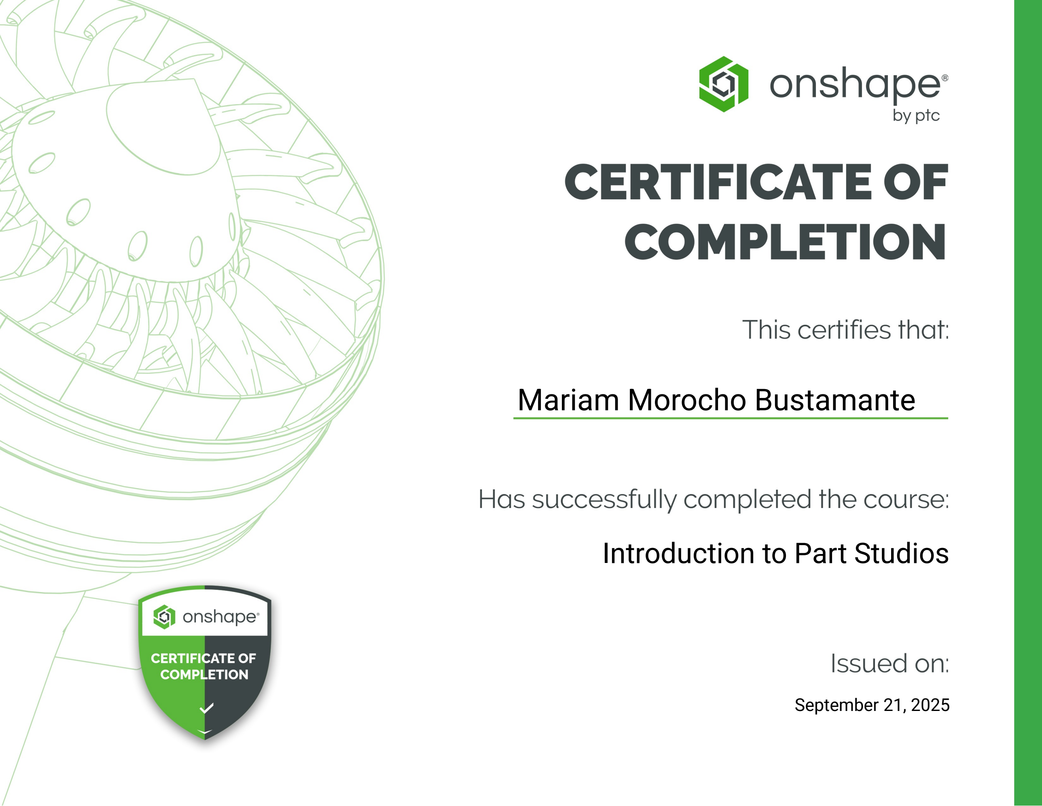
[picture p83: page 1]

Mariam Morocho Bustamante

Introduction to Part Studios

September 21, 2025
