JHuinapi/Proyecto-biodise-o-13/Talleres/Morocho Bustamante, Mariam Michelle/MariamMorochoBustamante_IntroductionToSketching.pdf

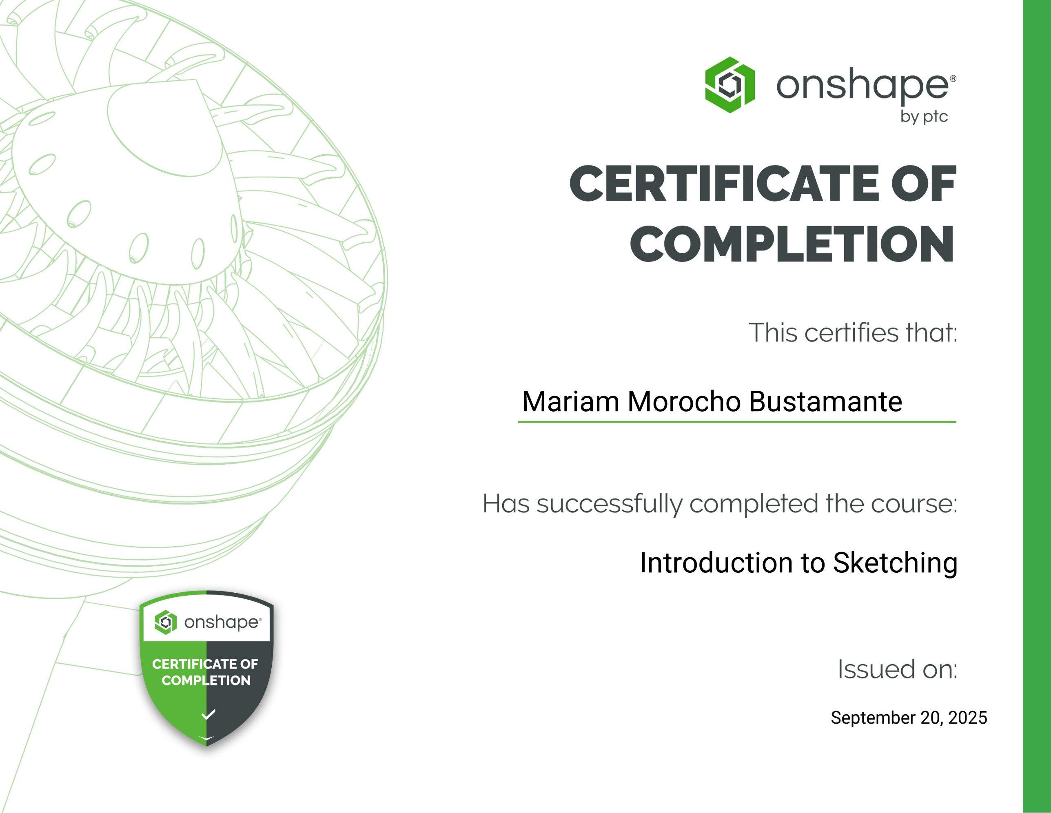
[picture p84: page 1]

Mariam Morocho Bustamante

Introduction to Sketching

September 20, 2025
