JHuinapi/Proyecto-biodise-o-13/Talleres/Morocho Bustamante, Mariam Michelle/MariamMorochoButsmante_Multi-PartPartStudio.pdf

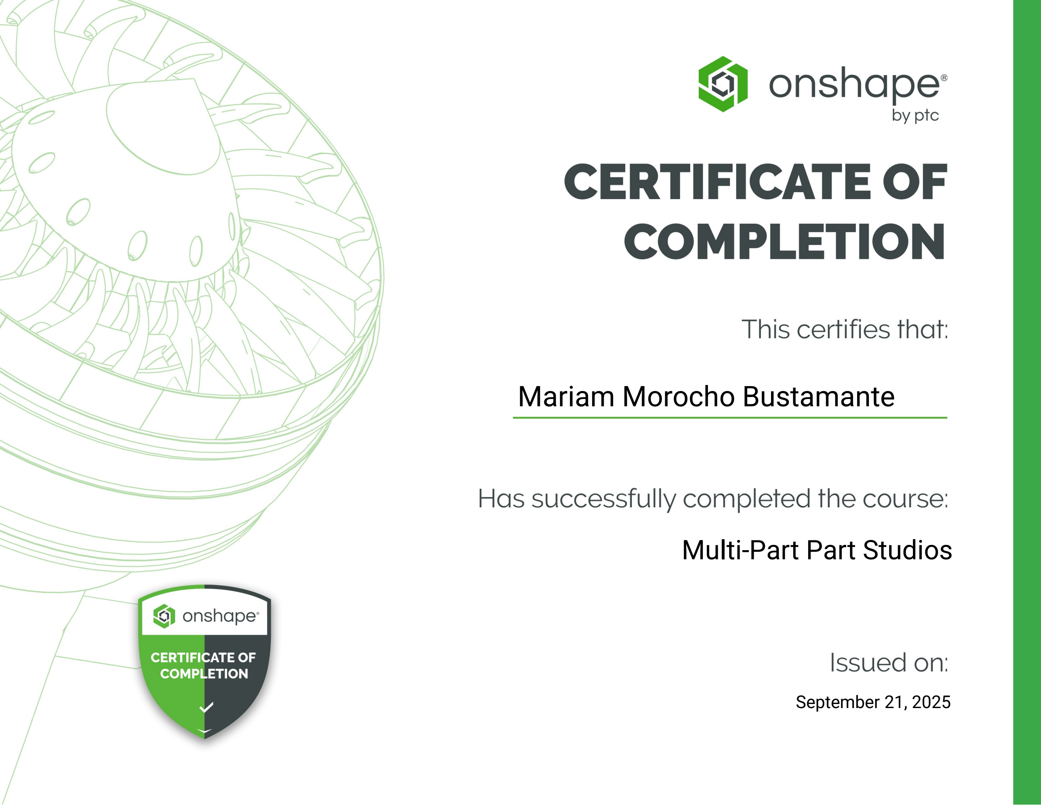
[picture p85: page 1]

Mariam Morocho Bustamante

September 21, 2025

Multi-Part Part Studios
