JHuinapi/Proyecto-biodise-o-13/Talleres/Mamani Casas Alexandra Milagros/AlexandraMamaniCasas_DetailedDrawings.pdf

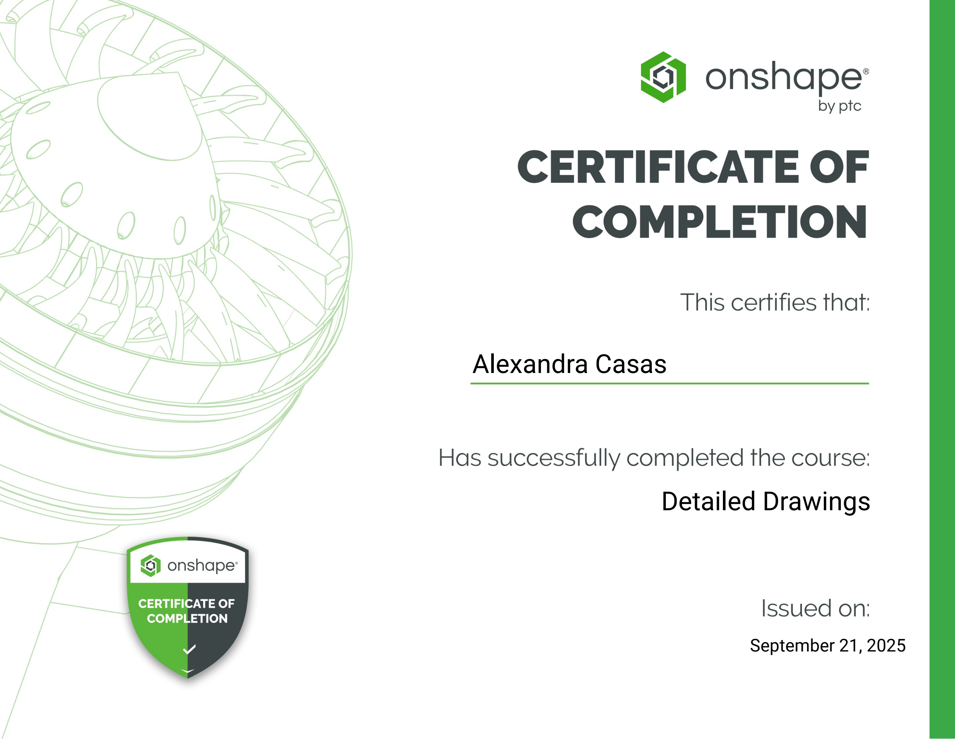
[picture p86: page 1]

Alexandra Casas

September 21, 2025

Detailed Drawings
