JHuinapi/Proyecto-biodise-o-13/Talleres/Mamani Casas Alexandra Milagros/AlexandraMamaniCasas_IntroductionToPartStudios.pdf

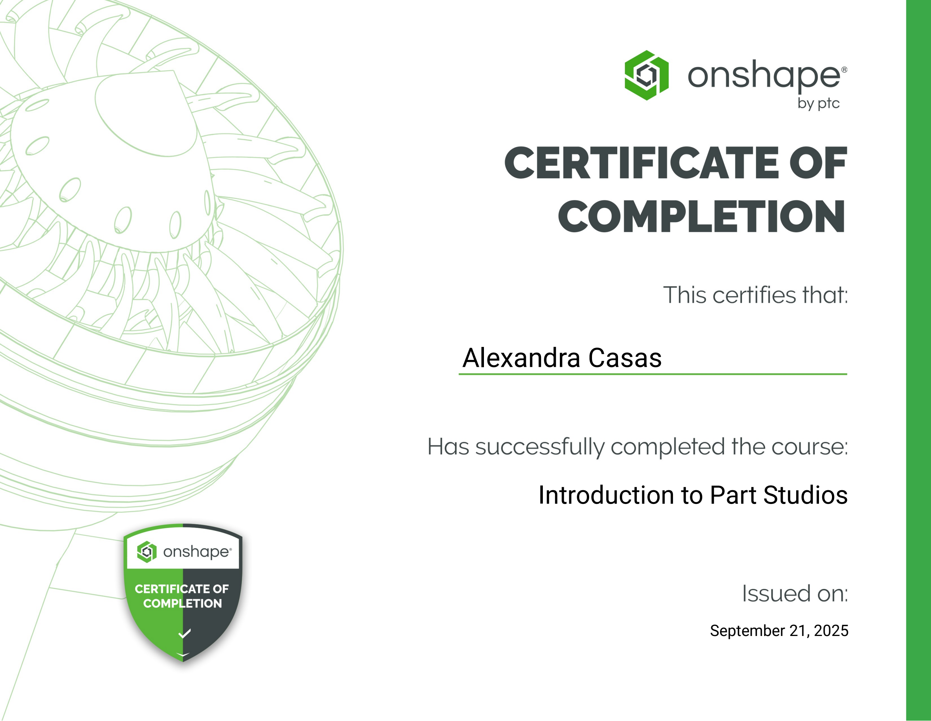
[picture p87: page 1]

Alexandra Casas

Introduction to Part Studios

September 21, 2025
