JHuinapi/Proyecto-biodise-o-13/Talleres/Mamani Casas Alexandra Milagros/AlexandraMamaniCasas_IntroductionToSketching.pdf

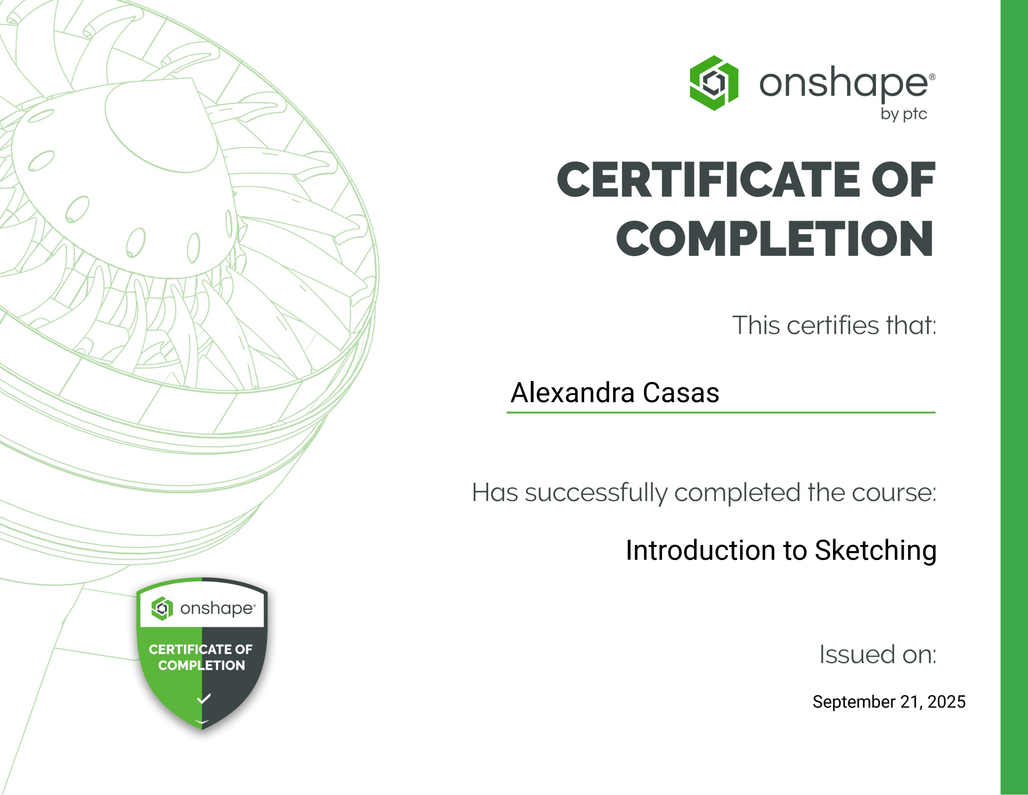
[picture p88: page 1]

Alexandra Casas

Introduction to Sketching

September 21, 2025
