JHuinapi/Proyecto-biodise-o-13/Talleres/Mamani Casas Alexandra Milagros/AlexandraMamaniCasas_MultiPartPartStudios.pdf

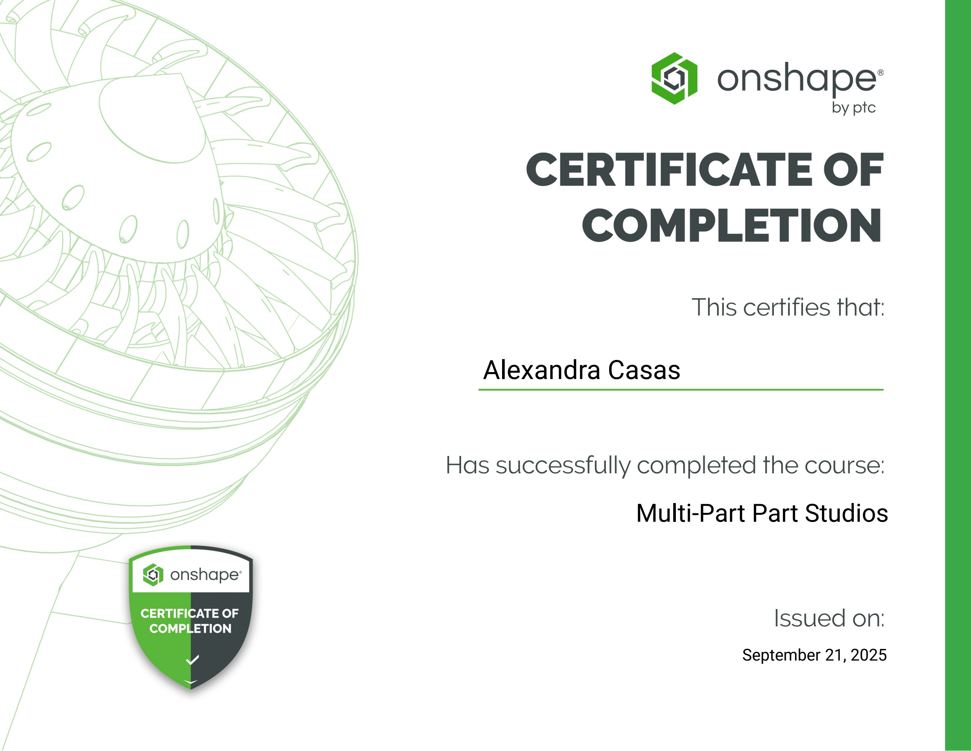
[picture p89: page 1]

Alexandra Casas

September 21, 2025

Multi-Part Part Studios
