JHuinapi/Proyecto-biodise-o-13/Documentacion/Entregables/Entregable N°12/Entregable 12.pdf

## Entregable 12

### 1. Contexto de uso

El dispositivo permite activar el sistema de trabe y destrabe de rodilla de manera remota, el bloque actúa de bloqueo físico a la flexión del eje de la rodilla, en este caso se diseñó un recubrimiento que consta de dos partes y se encaja al bloque que ya posee la órtesis del paciente. El proceso de bloqueo se realizará mediante un botón de un control de radiofrecuencia ubicado en el soporte del bastón de apoyo, de modo que la activación del mecanismo esté al alcance del paciente. Al incluir este mecanismo, el dispositivo le da independencia para poder subir las escaleras sin requerir de una persona que realice el trabe y destrabe por él. Además, se incluiría un sensor IMU que sea fácilmente plegable al calzado del paciente que tiene cómo función saber cómo se da la pisada, el cual priorizará una pisada talón-pie y que brinde ayudar a mejorar su marcha. El usuario de la solución propuesta es el paciente, la idea sería que lo use en su día a día para poder ayudarlo a tener una mayor libertad de movimiento y poder mejorar su marcha.

### 2. Perfil de usuario

El caso clínico corresponde a un paciente con lesión medular completa, clasificada como tipo A, localizada a nivel de T10. La lesión se produjo a raíz de un accidente durante el ejercicio de sus funciones en un taller mecánico. Como consecuencia del traumatismo, el paciente presenta pérdida de movilidad y sensibilidad en ambas extremidades inferiores. No obstante, gracias a la presencia de una zona de preservación parcial (ZPP), conserva cierto grado de movimiento y mantiene la función de los flexores de cadera y de rodilla, lo que le permite desplazarse con apoyo de bastones y un soporte ortésico situado a la altura de la rodilla que le ayuda a trabar la rodilla para realizar marchas en suelos continuos y destrabarla para la subir estructuras como escaleras. Actualmente, la lesión condiciona una marcha muy limitada, ya que el paciente requiere accionar manualmente los soportes ortésicos para poder realizar las flexiones o bloqueos articulares necesarios en su desplazamiento. Este mecanismo, aunque le brinda estabilidad, resulta poco práctico, pues cada vez que necesita subir o bajar estructuras, requiere la ayuda de terceros, lo que le arrebata la autonomía en su movilidad personas generando una dependencia significativa en sus actividades cotidianas y una incapacidad de volver a su trabajo anterior, al no contar con la movilidad que poseía anteriormente.

### 3. Análisis de tareas

Tareas | Riesgos
Calibración: - Para el sensor (MPU 9250) se debe establecer una posición de referencia y el rango de movimiento. | Mediciones erróneas al no establecer bien la posición de referencia y rango en el caso del sensor IMU. - Mal funcionamiento del dispositivo. El micromotor en la rodilla podría causar movimientos bruscos y por lo mismo lesiones. - Deterioro de

- Se debe verificar que todos las partes del dispositivo estén correctamente conectadas, por ejemplo la señal del botón con el micromotor en la rodilla. | componentes electrónicos por las malas conexiones y la calibración incorrecta, y deterioro del recubrimiento del bloqueo
Montaje en el paciente: - Se coloca la ortesis modificada en la pierna del usuario - Se ajustan el velcro | - Movimientos no deseados en la articulación - Lesiones cutáneas o molestias por un mal ajuste
Entrenamiento: - Se familiariza al paciente con el sistema explicando como funciona la ortesis - Se practica el uso y cambio de los modos en un entorno controlado como un hospital y con supervisión de un profesional de la salud, apoyado del sistema visual de reeducación. - Se pasa a practicar en terrenos más variados e irregulares en lugares que frecuente en su vida diaria. | - El paciente no comprendería en su totalidad el funcionamiento de la ortesis en un inicio. - Al no practicar suficientemente o adecuadamente, el paciente podría caerse o realizar movimientos erráticos que resulten en lesiones.
Desmontaje y limpieza: - El paciente se quita la ortesis. - Se realiza el mantenimiento de los componentes electrónicos y mecánicos. - Se revisa que las partes del dispositivo no estén desgastadas | - Un mal mantenimiento puede resultar en fallas al momento de usar el dispositivo lo que comprometería el bienestar y la seguridad del paciente.

### 4. Criterios de éxito(requisitos de usabilidad)

Objetivos | Análisis | Métrica de eficacia
Eficacia | El circuito agregado a la ortesis logra destrabar y trabar cuando esta recibe la orden por el control | Verificar la respuesta del motor y la conexión que posee el módulo con el arduino.
Eficiencia | El trabe y destrabe es realizado correctamente y no se presentan inconvenientes al momento de accionarse los motores | Cantidad de bloqueos y tiempo en el que se completa un ciclo de subida y bajada de la pieza de bloqueo
Satisfacción | Comodidad del usuario al usar la adaptación realizada a la ortesis que ya poseía | Comentarios y “feedbacks” del usuario, respecto a la comodidad, portabilidad y fiabilidad de la ortesis en el paciente.
Seguridad | No ha presentado situaciones de riesgo al usuario durante su uso | Lesiones del paciente al usar la ortesis modificada o heridas causadas por esta.

### 5. Diagrama esquemático corregido

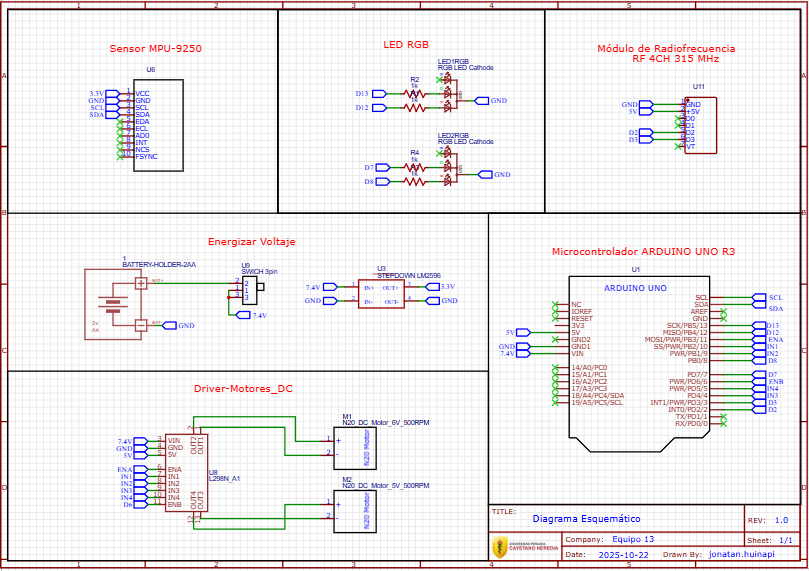
[picture p90: figure]

### 6. Modelado 3D

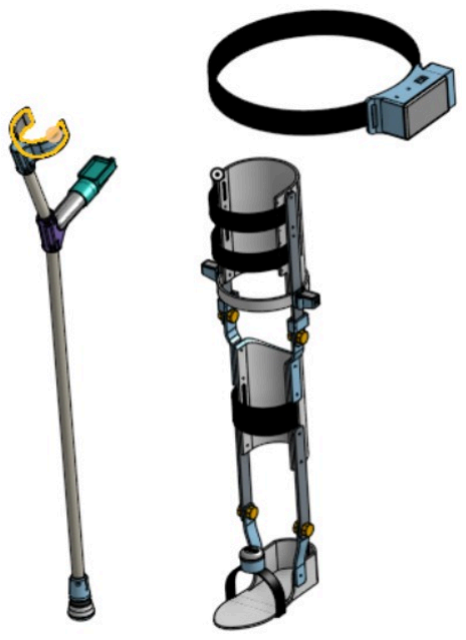
[picture p91: figure]
