JHuinapi/Proyecto-biodise-o-13/Documentacion/Entregables/Entregable N°9/Entregable 9.pdf

## Entregable 9

Avance del Prototipado electrónico

### 1. Diagrama esquemático corregido

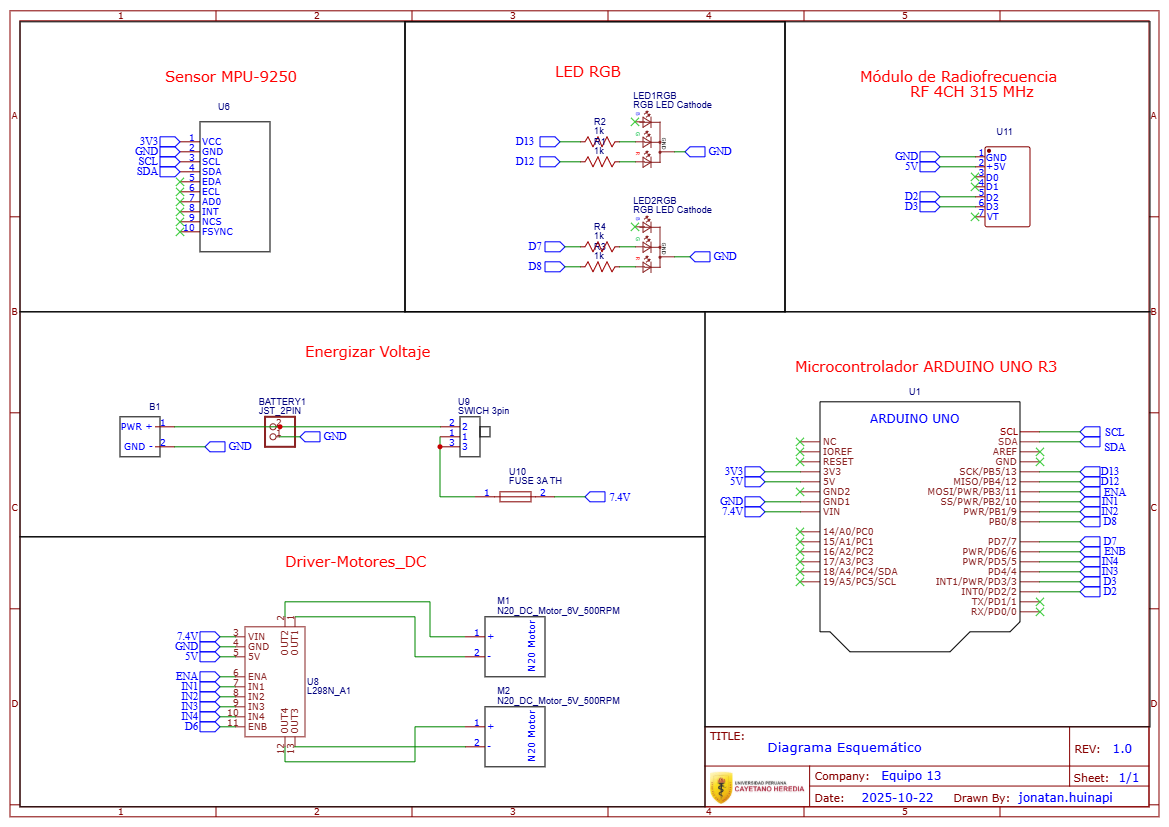
[picture p95: figure]

### 2. Avance del prototipado electrónico

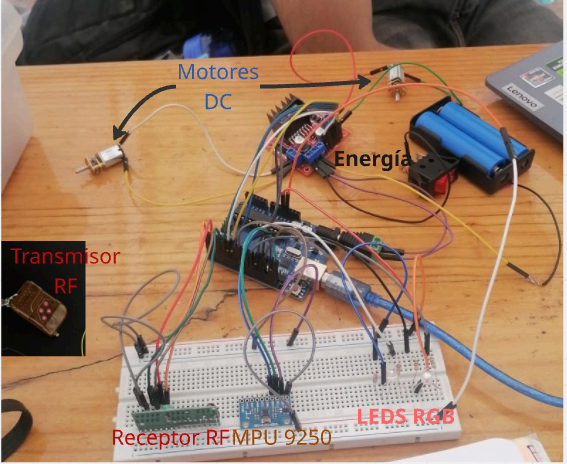
[picture p96: figure]

Plan de usabilidad basado en evidencias.

### 1. Contexto de uso

El dispositivo permite activar el sistema de trabe y destrabe de rodilla mediante un botón de un control de radiofrecuencia ubicado en el apoyo del bastón. Al incluir este mecanismo, el dispositivo le da independencia para poder subir las escaleras sin requerir de una persona que realice el trabe y destrabe por él. Además, se incluiría un sensor IMU que sea fácilmente plegable al calzado del paciente que tiene cómo función saber cómo se da la pisada, el cual priorizará una pisada talón-pie y que brinde ayudar a mejorar su marcha.
El usuario de la solución propuesta es el paciente, la idea sería que lo use en su día a día para poder ayudarlo a tener una mayor libertad de movimiento y poder mejorar su marcha.

Modelado 3D:

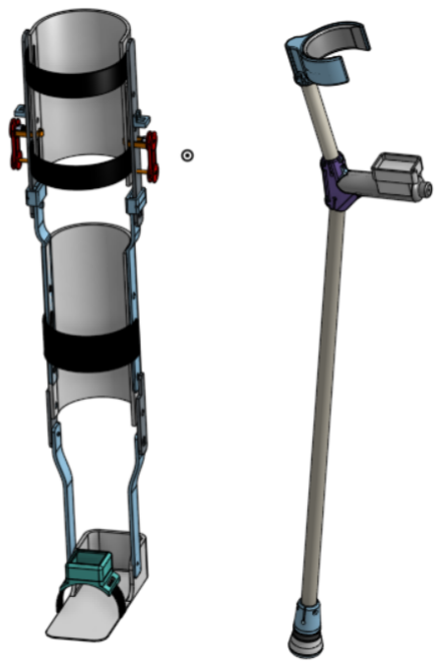
[picture p97: figure]

Enlace one shape:
https://cad.onshape.com/documents/9151631e7d9ce6ed4cfbf4c8/w/7290ecdbfc1a44e7acb436d5/e/5eba89453f18ad0daa43656c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 (https://cad.onshape.com/documents/9151631e7d9ce6ed4cfbf4c8/w/7290ecdbfc1a44e7acb436d5/e/5eba89453f18ad0daa43656c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)

### 2. Perfil del usuario

El caso clínico corresponde a un paciente con lesión medular completa, clasificada como tipo A, localizada a nivel de T10. La lesión se produjo a raíz de un accidente durante el ejercicio de sus funciones en un taller mecánico. Como consecuencia del traumatismo, el paciente presenta pérdida de movilidad y sensibilidad en ambas extremidades inferiores. No obstante, gracias a la presencia de una zona de preservación parcial (ZPP), conserva cierto grado de movimiento y mantiene la función de los flexores de cadera, lo que le permite desplazarse con apoyo de bastones y un soporte ortésico situado a la altura de la rodilla que le ayuda a trabar la rodilla para realizar marchas en suelos continuos y destrabarla para la subir estructuras como escaleras.
Actualmente, la lesión condiciona una marcha muy limitada, ya que el paciente requiere accionar manualmente los soportes ortésicos para poder realizar las flexiones o bloqueos articulares necesarios en su desplazamiento. Este mecanismo, aunque le brinda estabilidad, resulta poco práctico, pues cada vez que necesita subir o bajar estructuras, requiere la ayuda de terceros, lo que le arrebata la autonomía en su movilidad personas generando una dependencia significativa en sus actividades cotidianas y una incapacidad de volver a su trabajo anterior, al no contar con la movilidad que poseía anteriormente.

### 3. Análisis de tareas

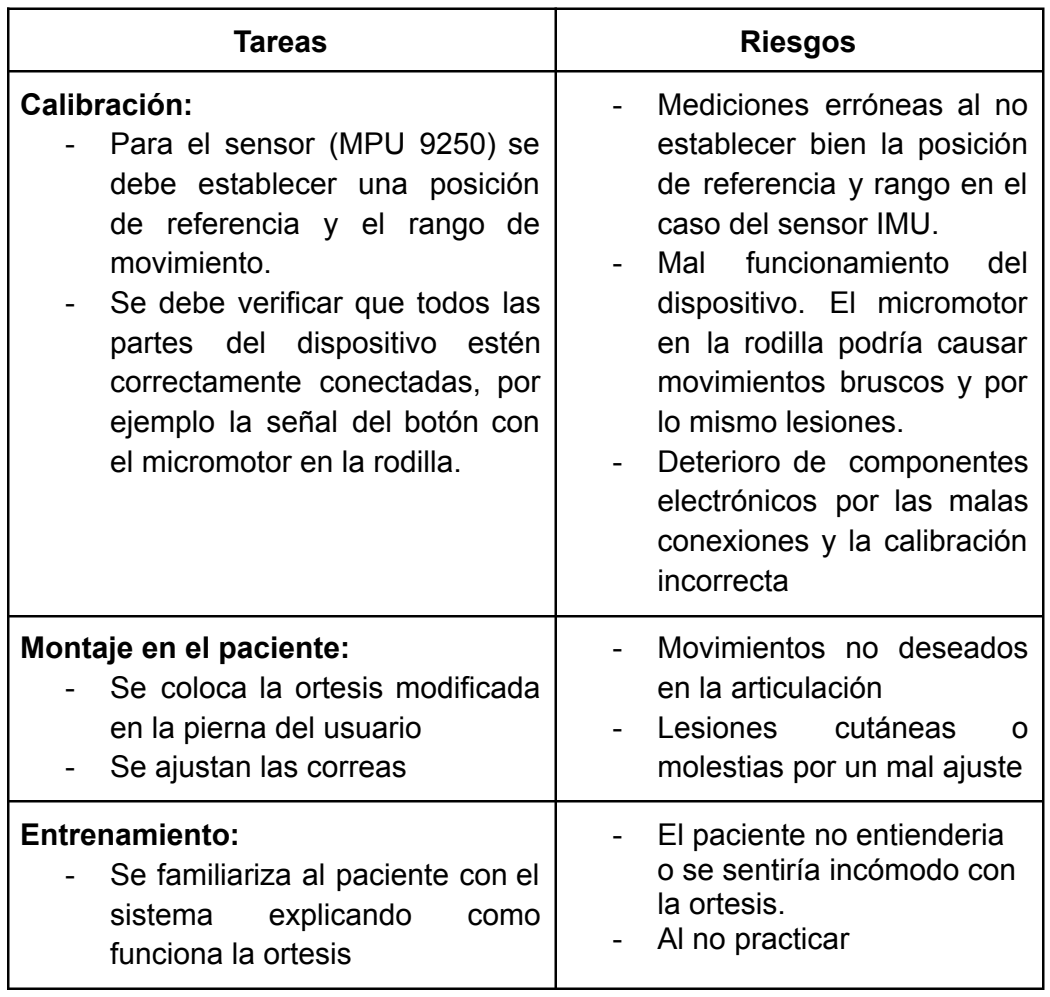
[picture p98: figure]
Tareas; Riesgos; Calibración: - Para el sensor (MPU 9250) se debe establecer una posición de referencia y el rango de movimiento. - Se debe verificar que todos las partes del dispositivo estén correctamente conectadas, por ejemplo la señal del botón con el micromotor en la rodilla.; - Mediciones erróneas al no establecer bien la posición de referencia y rango en el caso del sensor IMU.; - Mal; funcionamiento del; dispositivo. El micromotor en la rodilla podría causar movimientos bruscos y por lo mismo lesiones. - Deterioro de componentes electrónicos por las malas conexiones y la calibración incorrecta; Montaje en el paciente: - Se coloca la ortesis modificada en la pierna del usuario - Se ajustan las correas; - Movimientos no deseados en la articulación; - Lesiones; cutáneas; molestias por un mal ajuste; Entrenamiento: - Se familiariza al paciente con el; sistema; explicando; como; funciona la ortesis; - El paciente no entienderia o se sentiría incómodo con la ortesis. - Al no practicar

- Se practica el uso y cambio de los modos en un entorno controlado como un hospital y con supervisión de un profesional de la salud. - Se pasa a practicar en terrenos más variados e irregulares en lugares que frecuente en su vida diaria. | suficientemente o adecuadamente, el paciente podría caerse o realizar movimientos erróneos que resulten en lesiones.
Desmontaje y limpieza: - El paciente se quita la ortesis. - Se realiza el mantenimiento de los componentes electrónicos. - Se revisa que las partes del dispositivo no estén desgastadas. | - Un mal mantenimiento puede resultar en fallas al momento de usar el dispositivo lo que comprometería el bienestar del paciente.

### 4. Criterios de éxito (requisitos de usabilidad)

Objetivos | Análisis | Métrica de eficacia
Eficacia | El circuito agregado a la ortesis logra destrabar y trabar cuando esta recibe la orden por el control | Verificar la respuesta y conexión que posee el módulo con el arduino.
Eficiencia | El trabe y destrabe es realizado correctamente y no se presentan inconvenientes al momento de accionarse los motores | Tiempo en el que se completa un ciclo de subida y bajada de la pieza de bloqueo
Satisfacción | Comodidad del usuario al usar la adaptación realizada a la ortesis que ya poseía | comentarios y “feedbacks” del usuario, respecto a la comodidad, portabilidad y fiabilidad de la ortesis en el paciente.
seguridad | No ha presentado situaciones de riesgo al usuario durante su uso | Lesiones del paciente al usar la ortesis o heridas causadas por esta.
