JHuinapi/Proyecto-biodise-o-13/Talleres/Murillo Sedano Ricardo Sebastián/Detailed Drawings.pdf

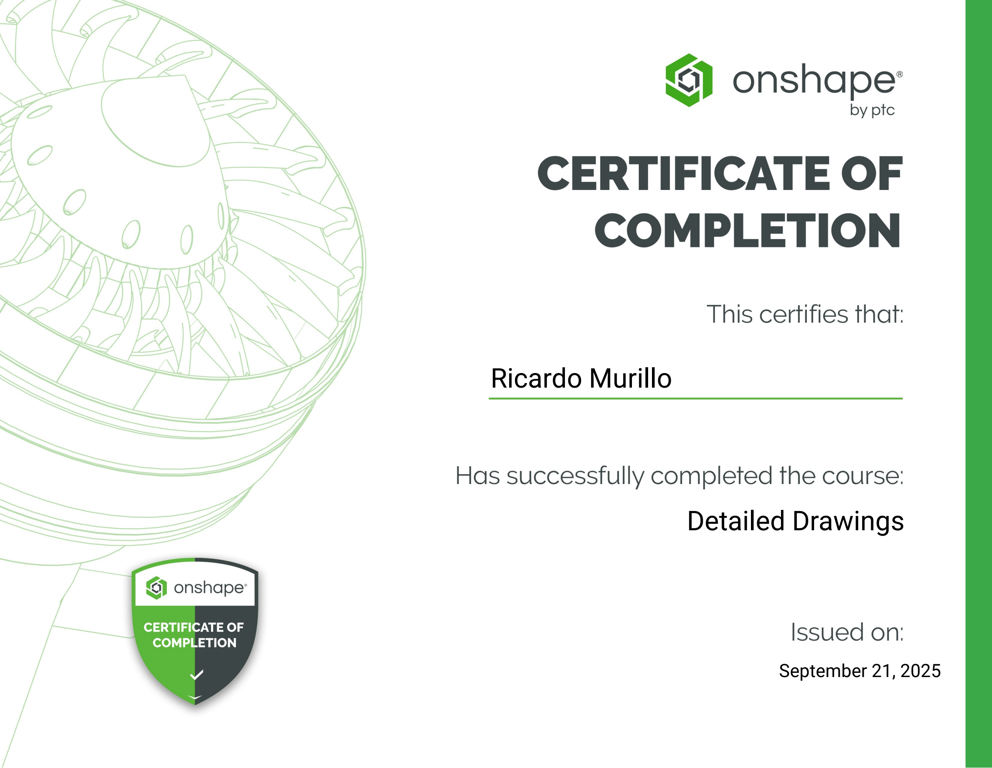
[picture p117: page 1]

Ricardo Murillo

September 21, 2025

Detailed Drawings
