JHuinapi/Proyecto-biodise-o-13/Talleres/Murillo Sedano Ricardo Sebastián/Introduction to Part Studios.pdf

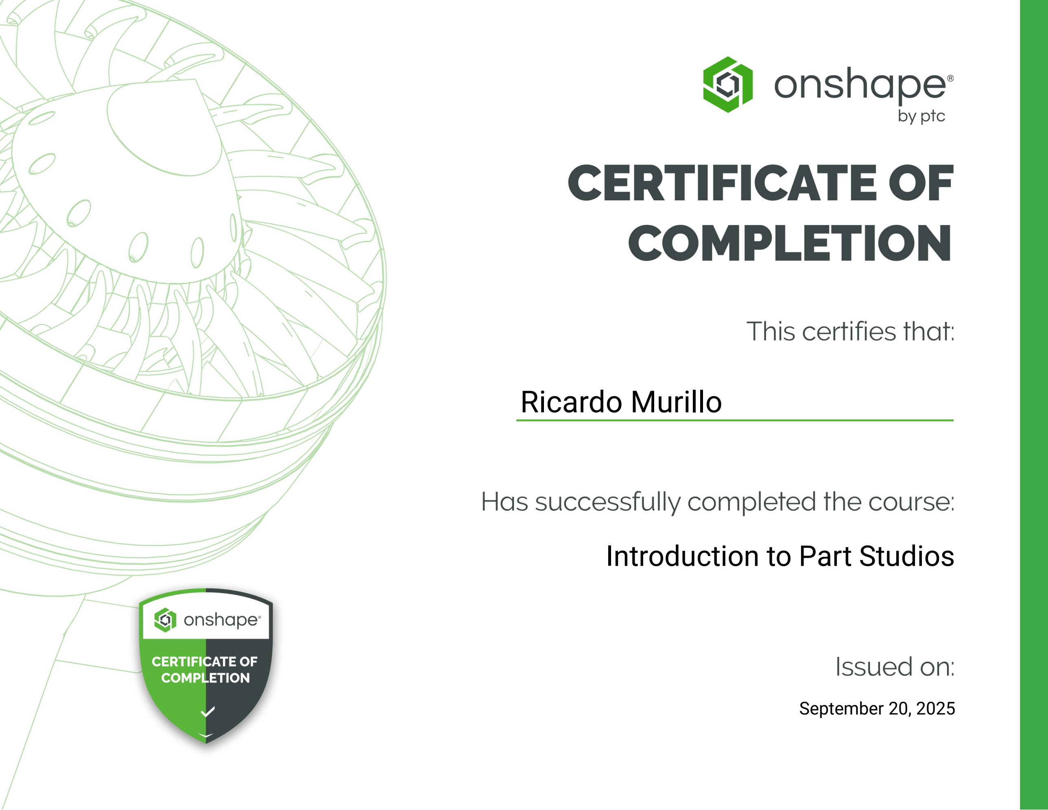
[picture p118: page 1]

Ricardo Murillo

Introduction to Part Studios

September 20, 2025
