JHuinapi/Proyecto-biodise-o-13/Talleres/Murillo Sedano Ricardo Sebastián/Introduction to Sketching.pdf

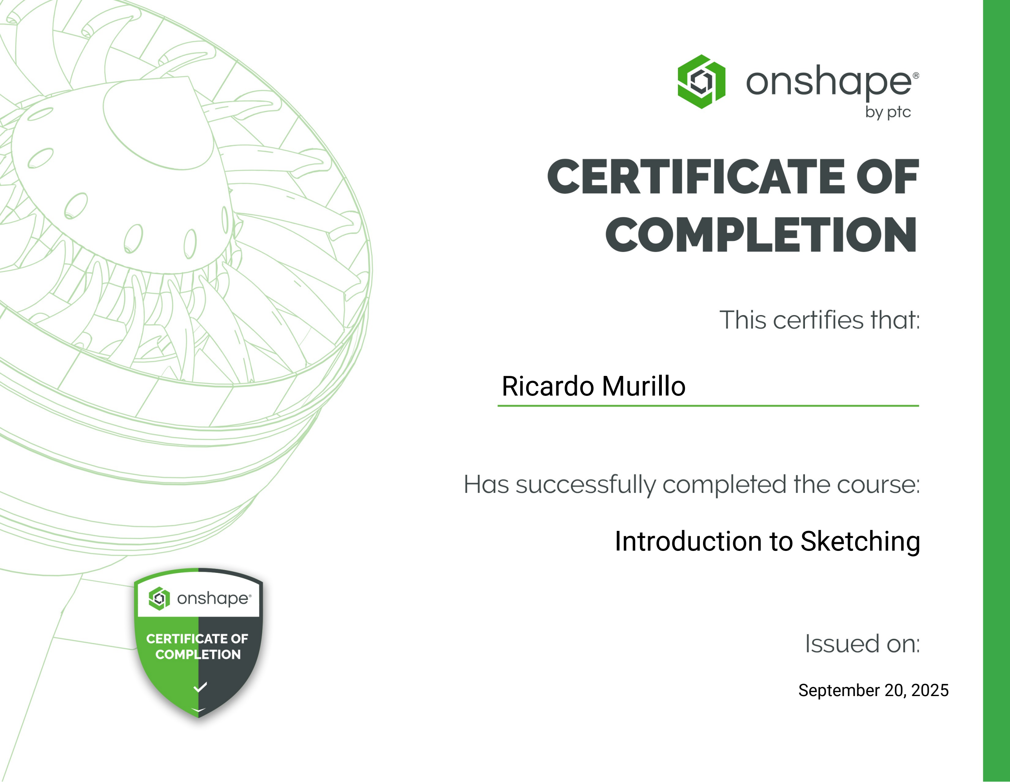
[picture p119: page 1]

Ricardo Murillo

Introduction to Sketching

September 20, 2025
