JHuinapi/Proyecto-biodise-o-13/Talleres/Murillo Sedano Ricardo Sebastián/Multi-Part Part Studios.pdf

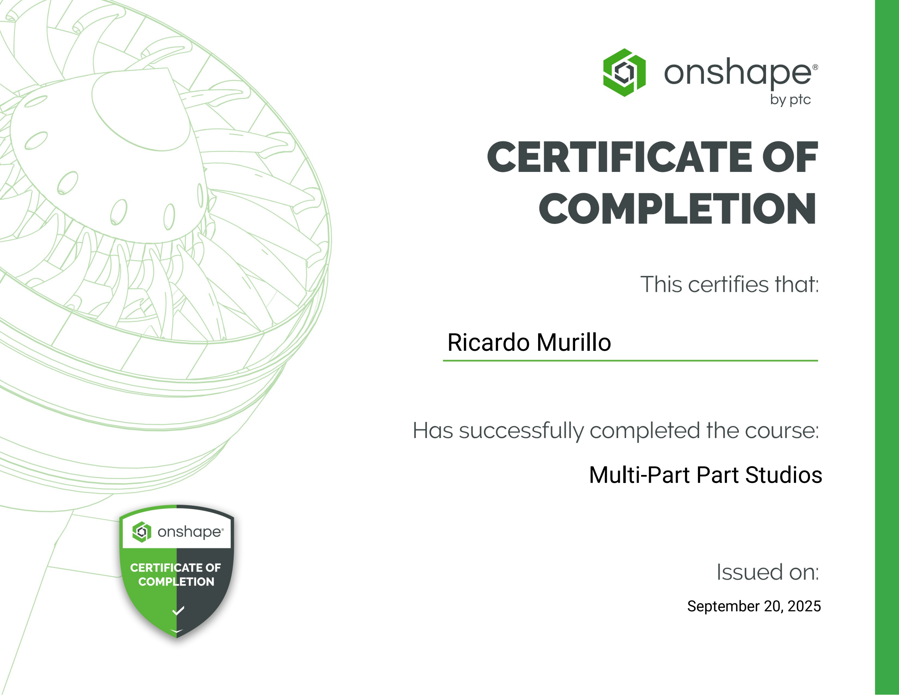
[picture p120: page 1]

Ricardo Murillo

September 20, 2025

Multi-Part Part Studios
