JHuinapi/Proyecto-biodise-o-13/Talleres/Murillo Sedano Ricardo Sebastián/Onshape Assemblies.pdf

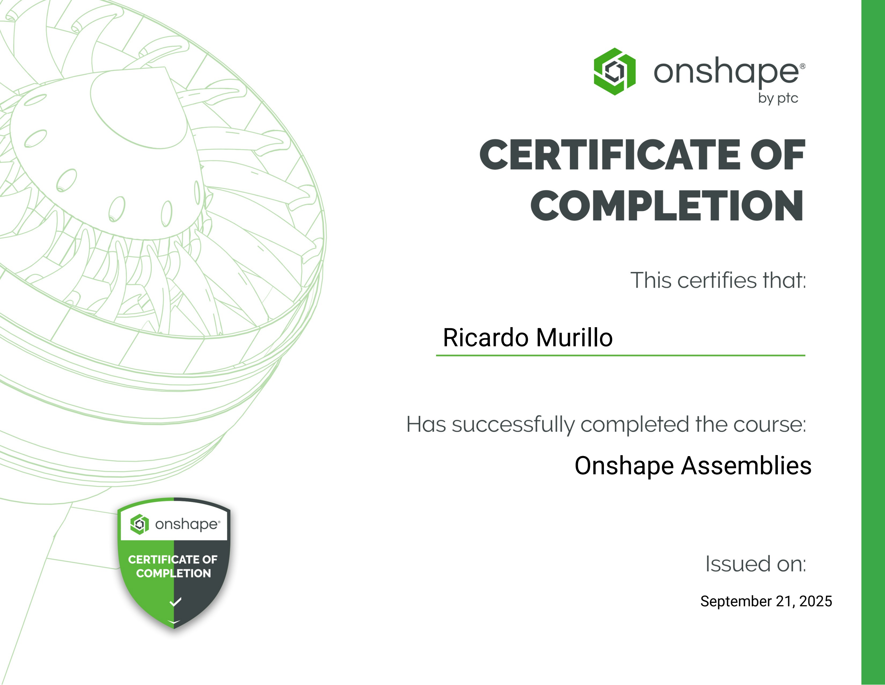
[picture p137: page 1]

Ricardo Murillo

September 21, 2025

Onshape Assemblies
