JHuinapi/Proyecto-biodise-o-13/Documentacion/Entregables/Entregable N°9/built/Caja componentes muslo (2).pdf

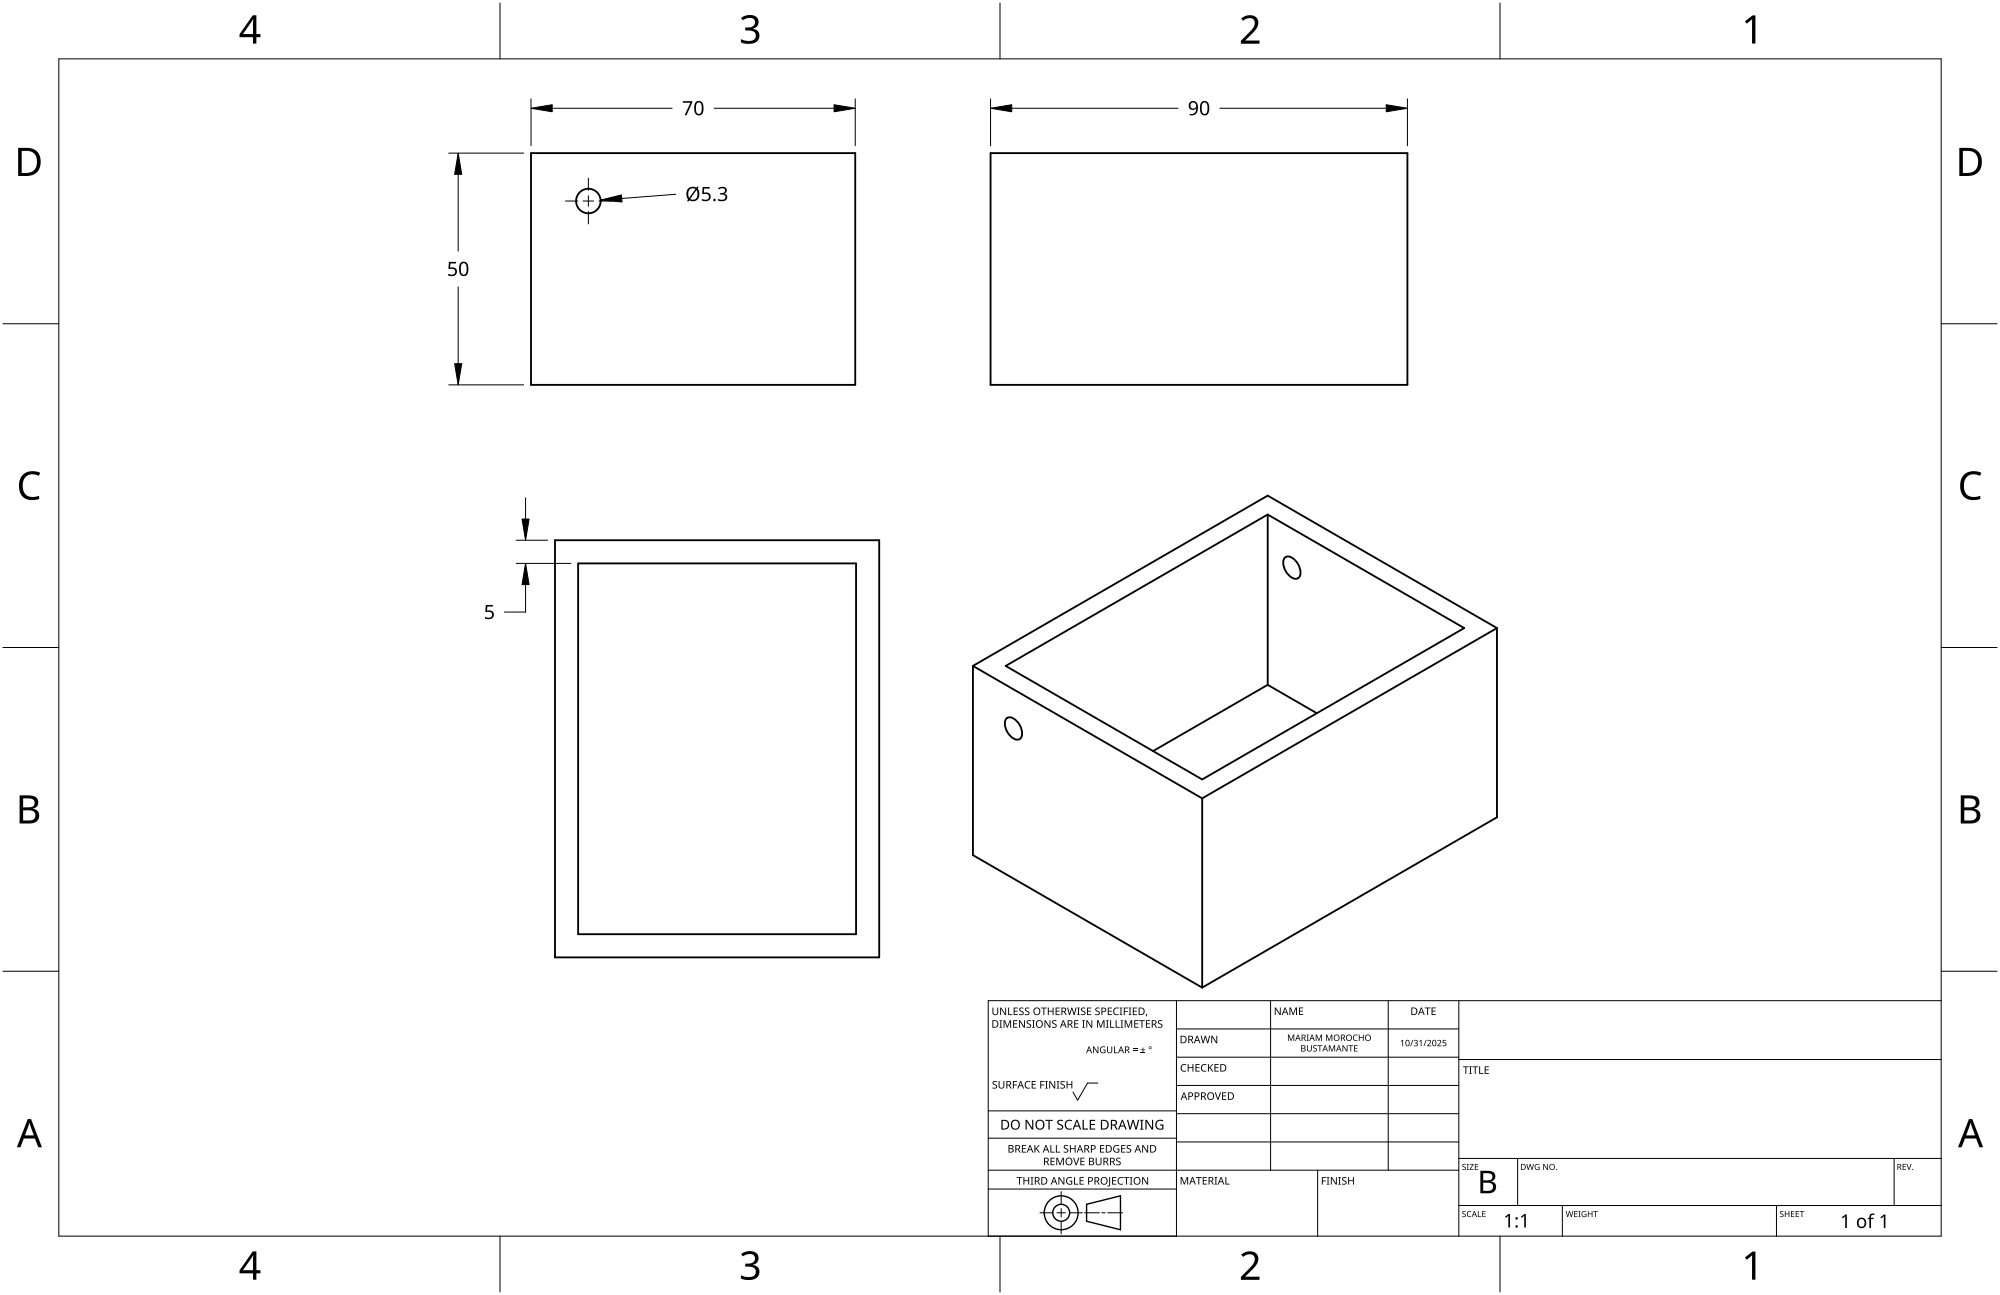
[picture p138: page 1]
