JHuinapi/Proyecto-biodise-o-13/Documentacion/Entregables/Entregable N°9/built/Dibujo caja de componentes.pdf

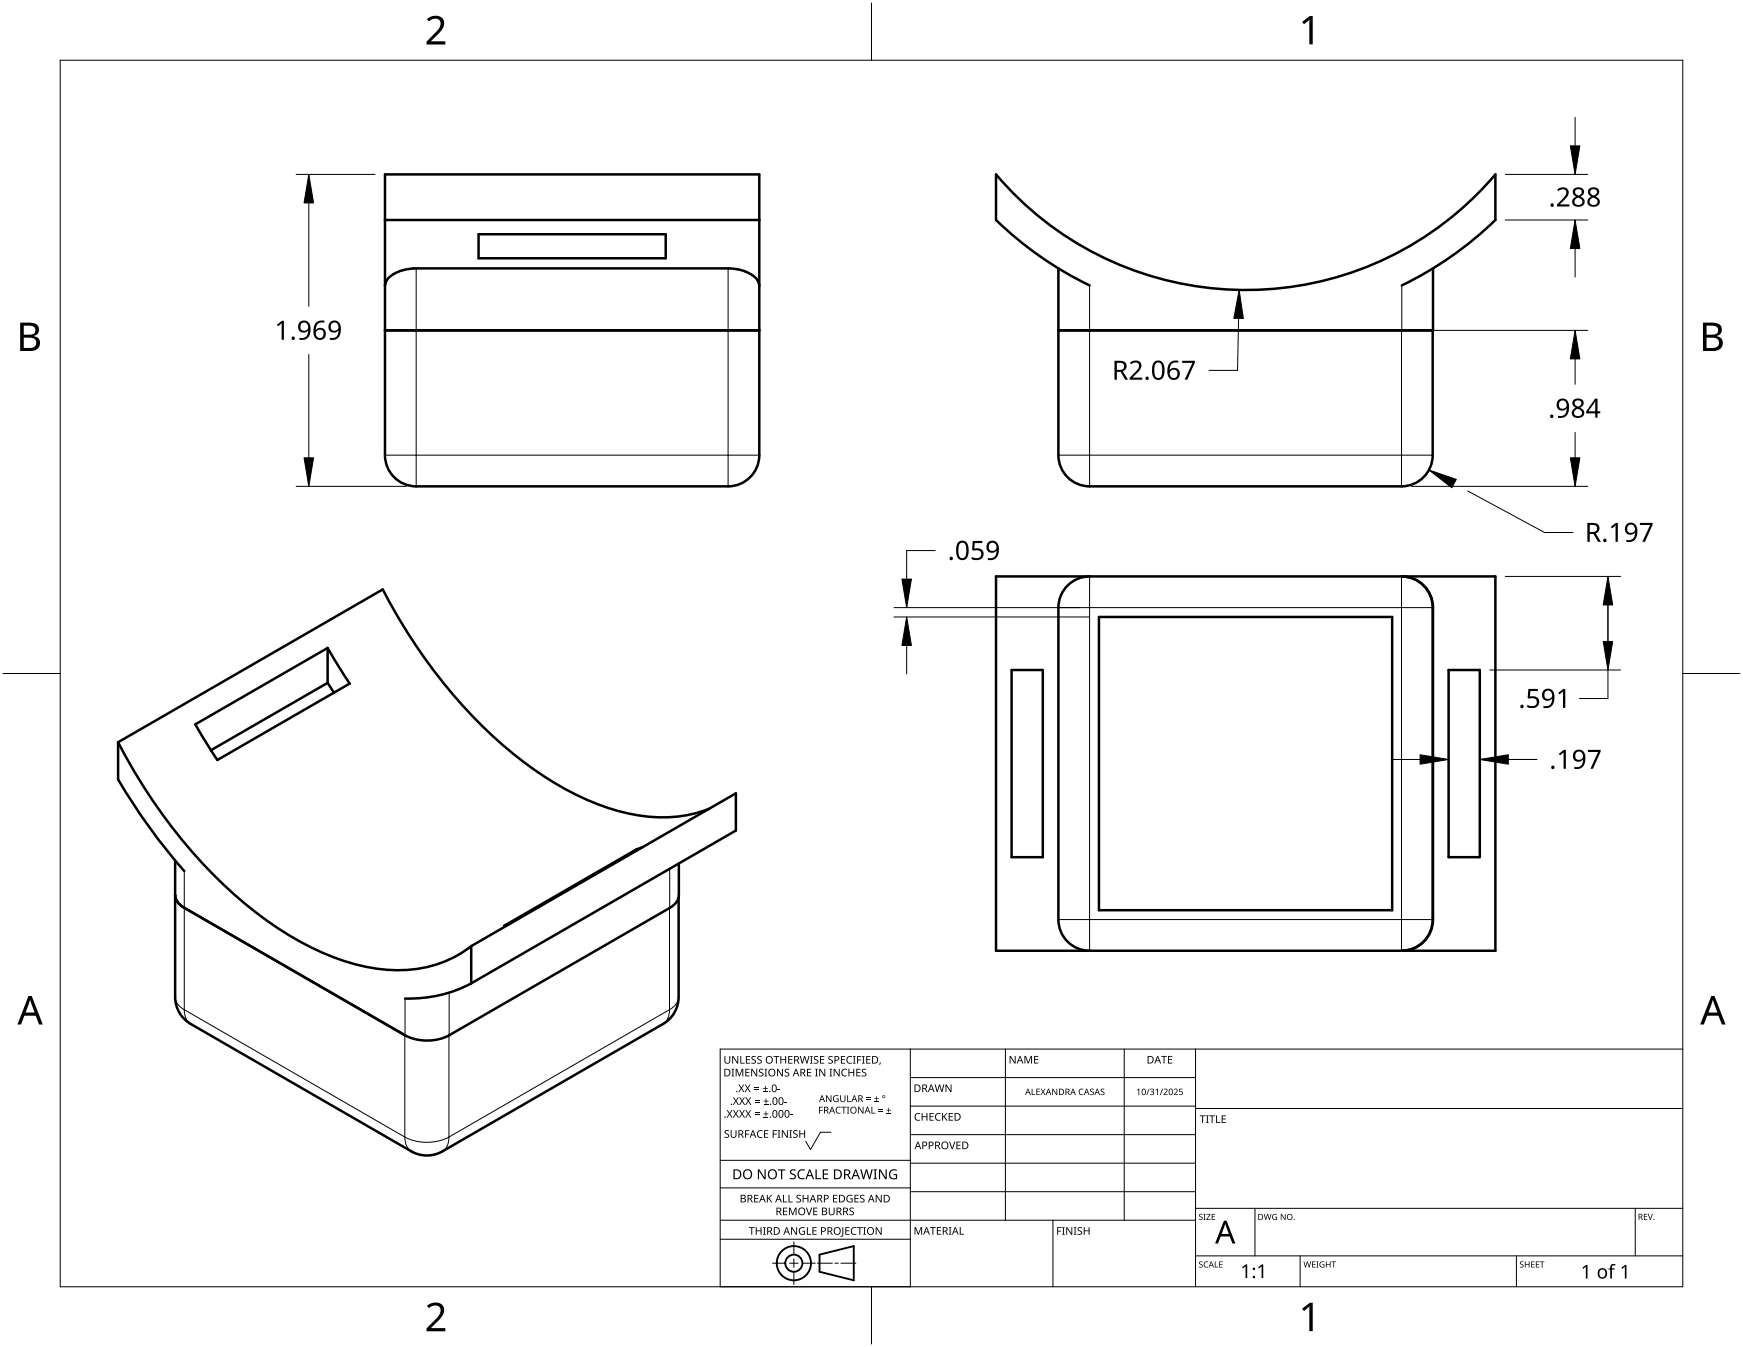
[picture p139: page 1]
