JHuinapi/Proyecto-biodise-o-13/Documentacion/Entregables/Entregable N°9/built/Dibujo boton carcasa.pdf

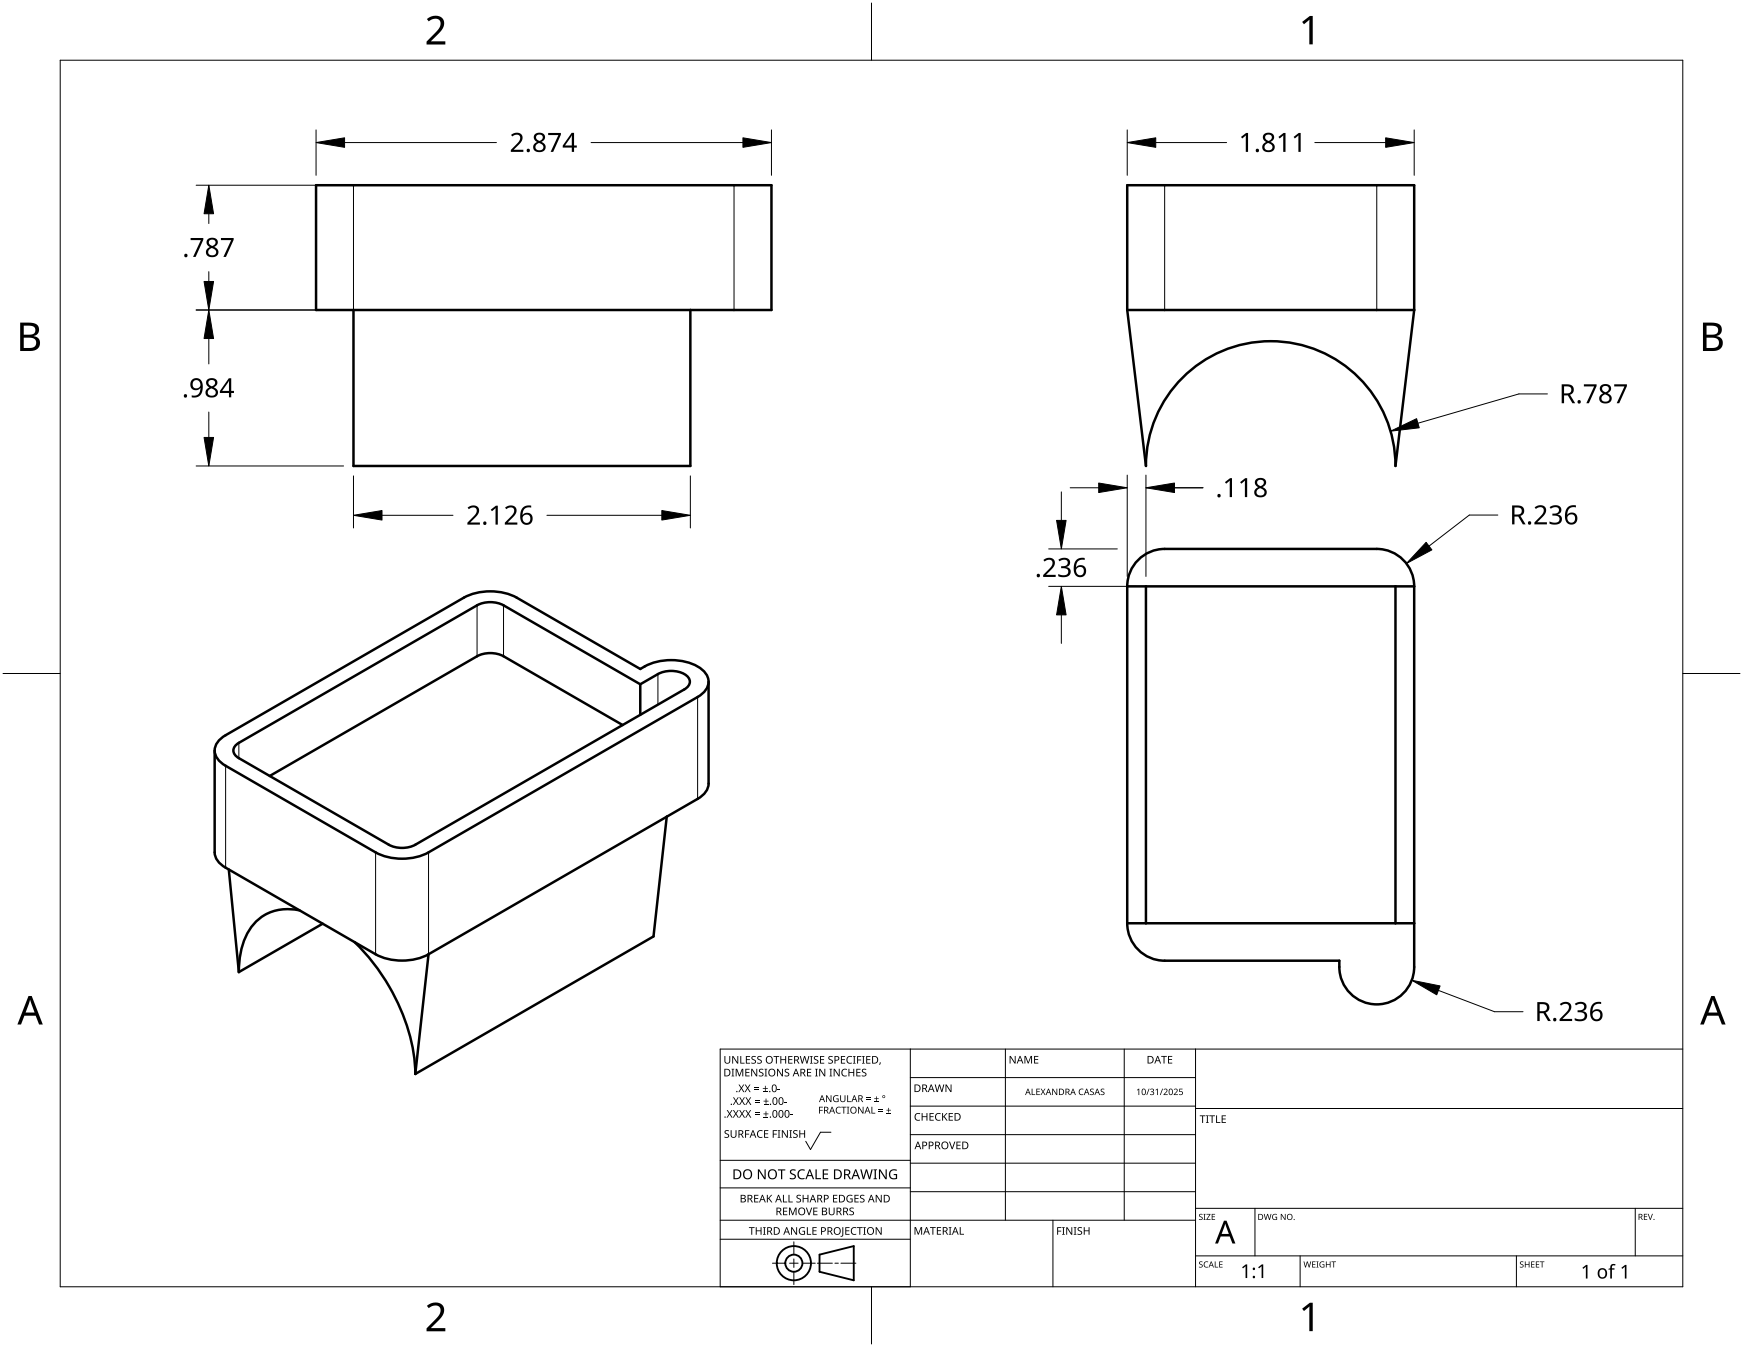
[picture p140: page 1]
