JHuinapi/Proyecto-biodise-o-13/Documentacion/Entregables/Entregable N°9/built/Dibujo muslo.pdf

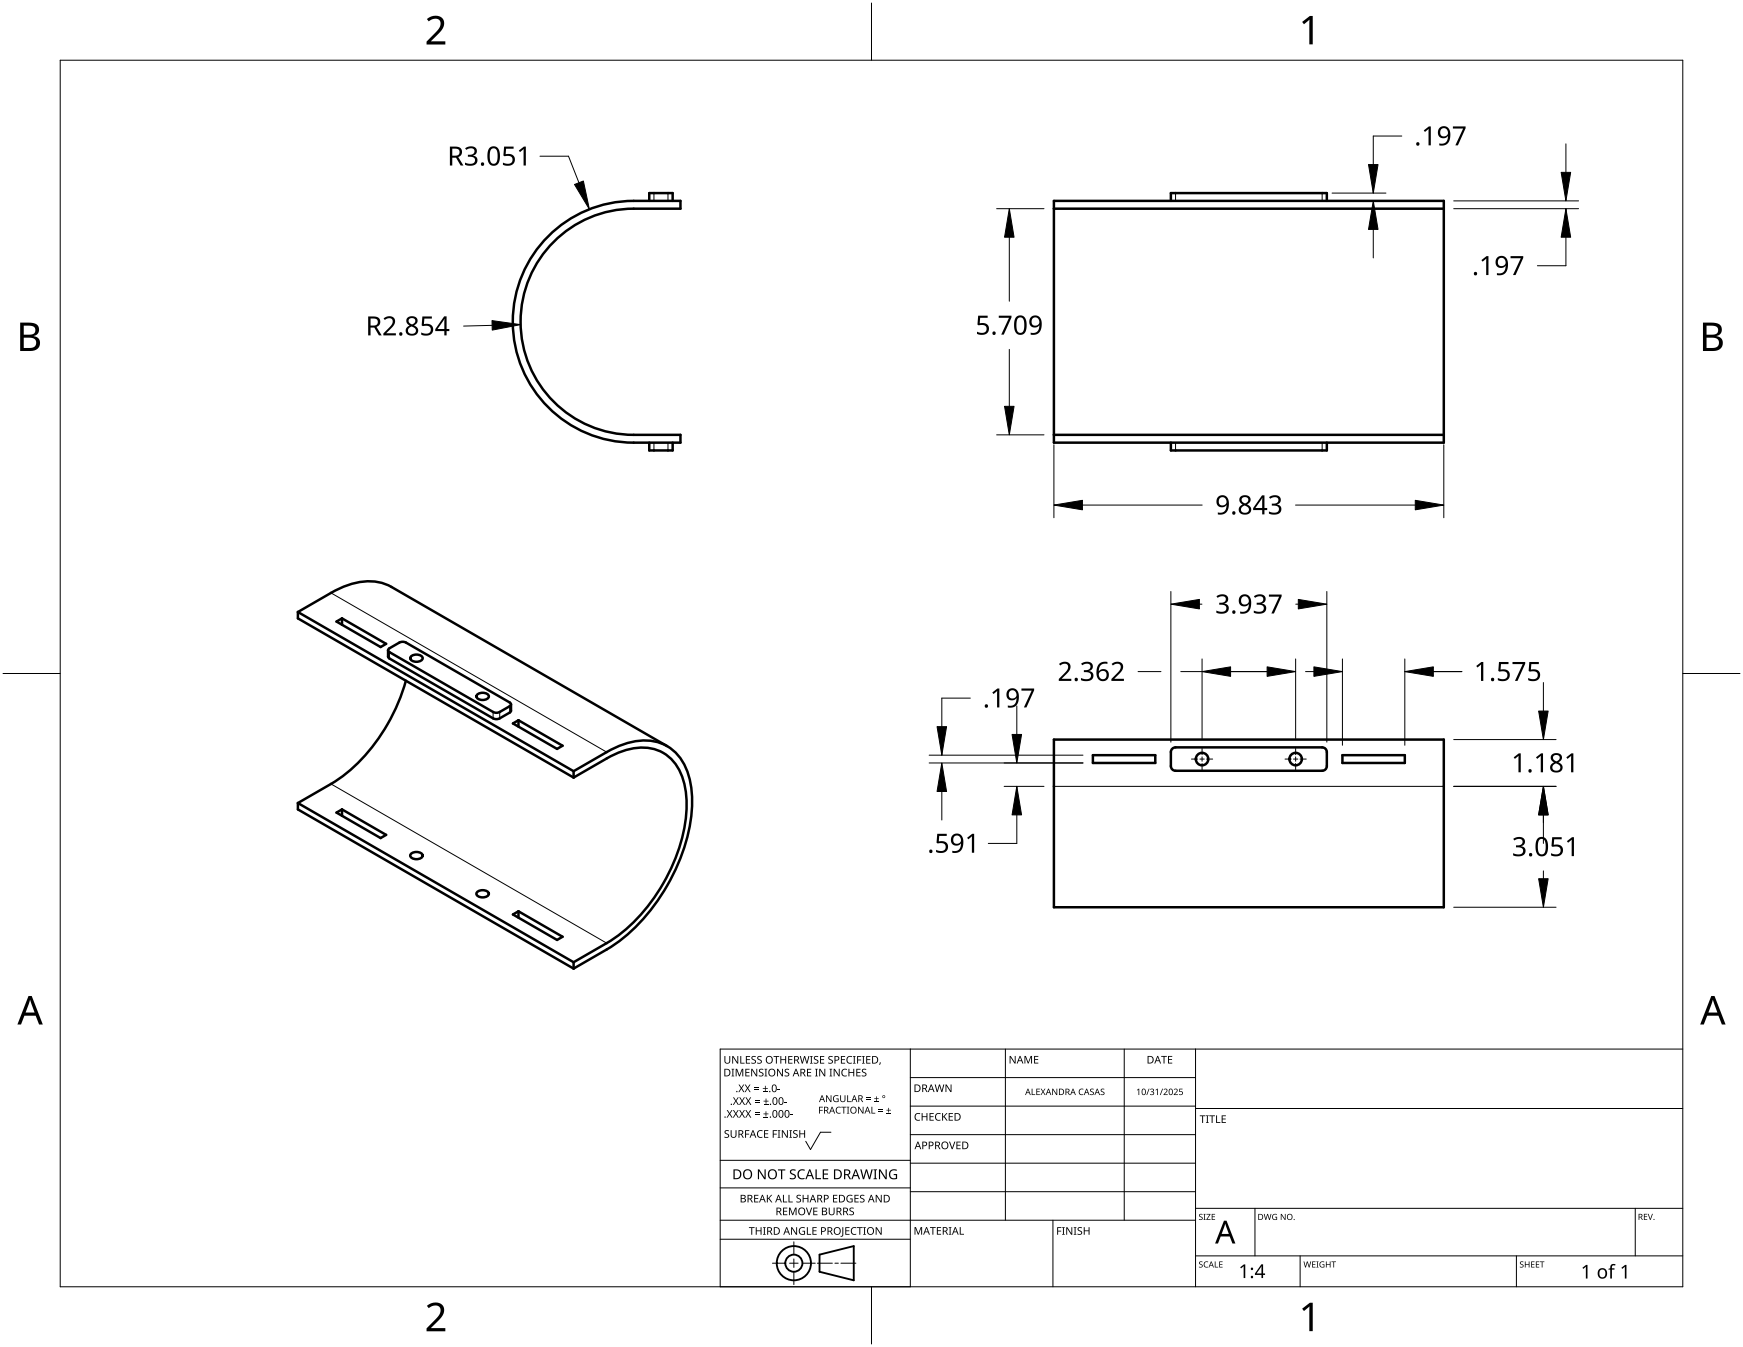
[picture p141: page 1]
