JHuinapi/Proyecto-biodise-o-13/Documentacion/Entregables/Entregable N°9/built/Dibujo pantorrilla.pdf

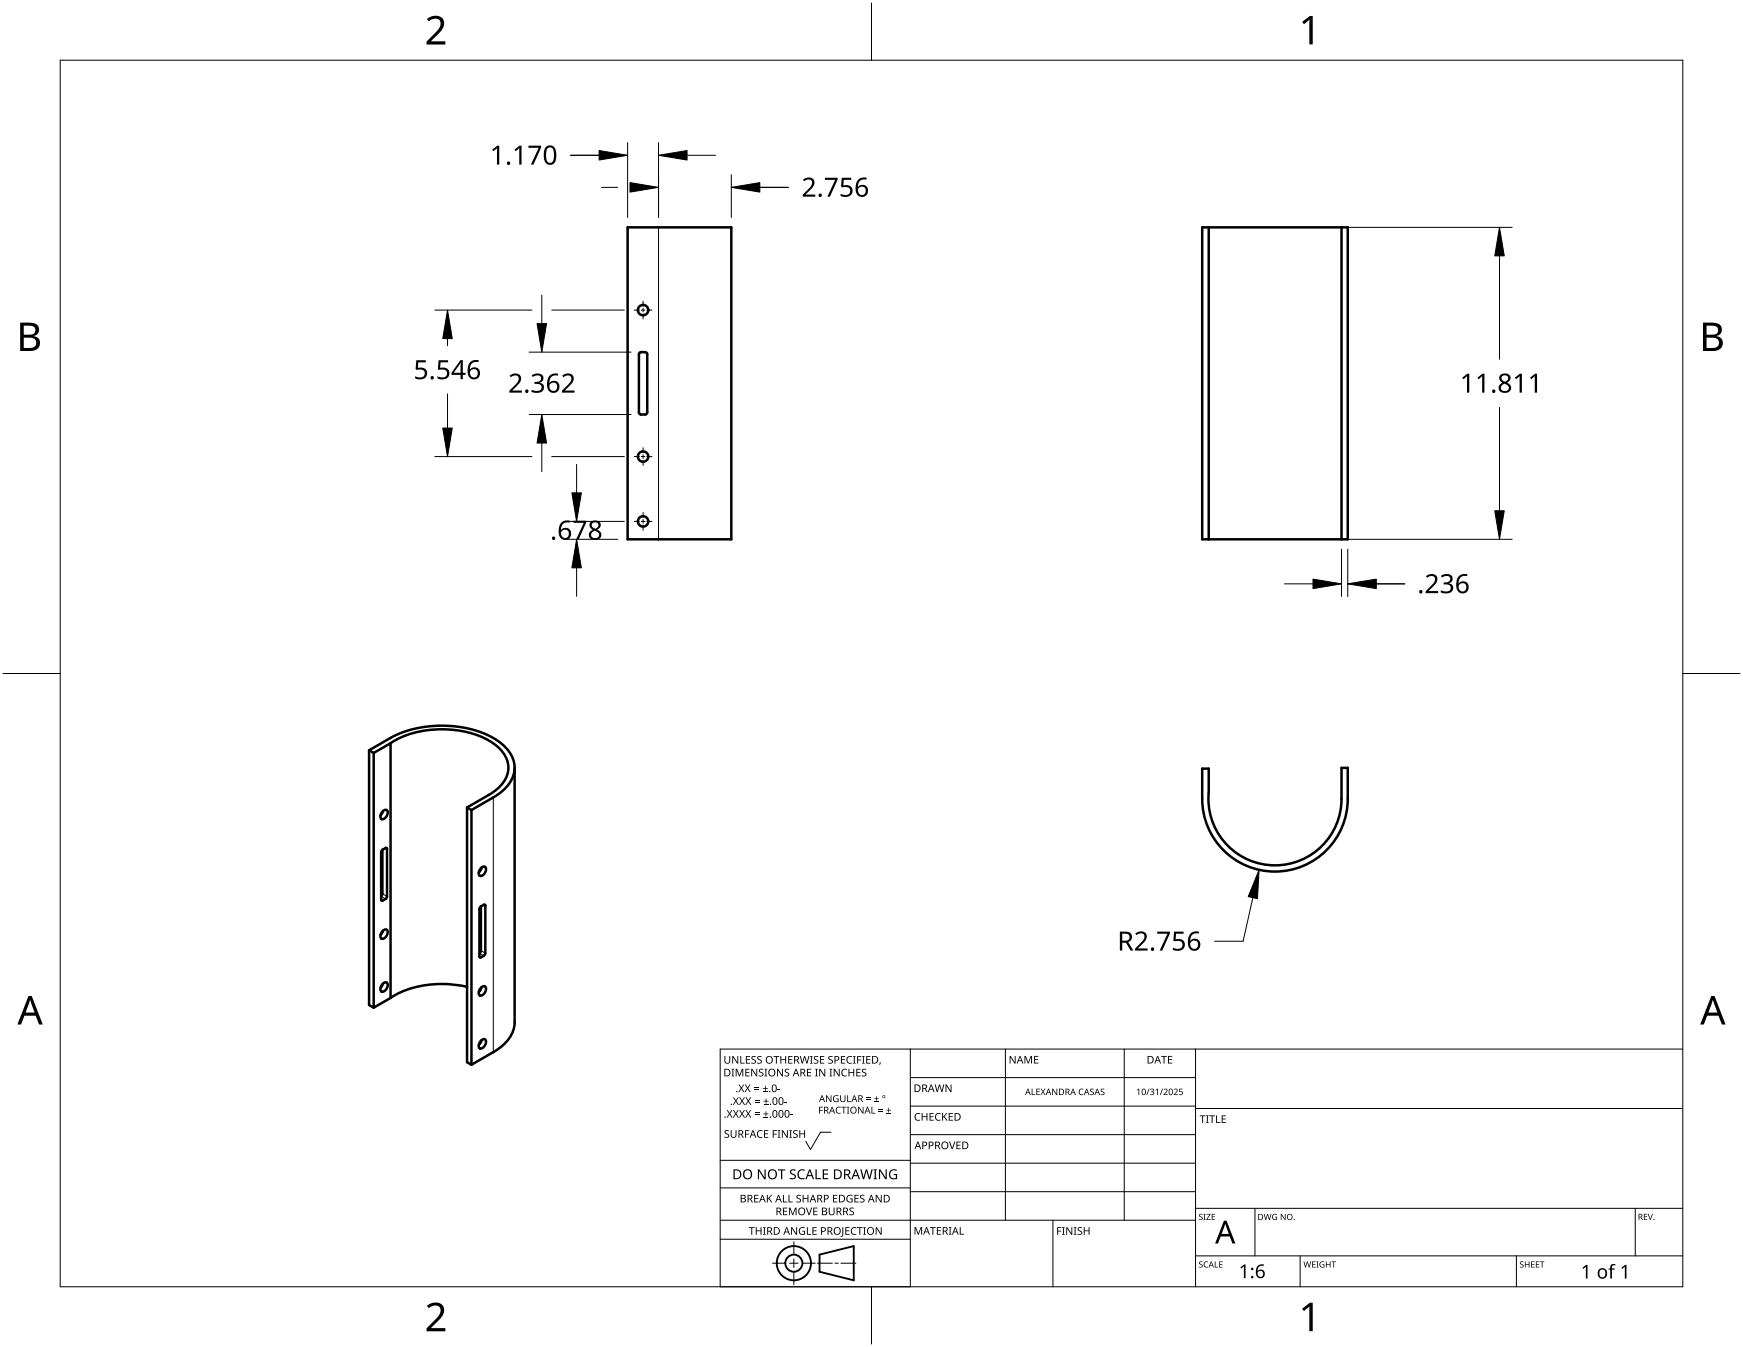
[picture p142: page 1]
