JHuinapi/Proyecto-biodise-o-13/Documentacion/Entregables/Entregable N°9/built/Dibujo parte pie.pdf

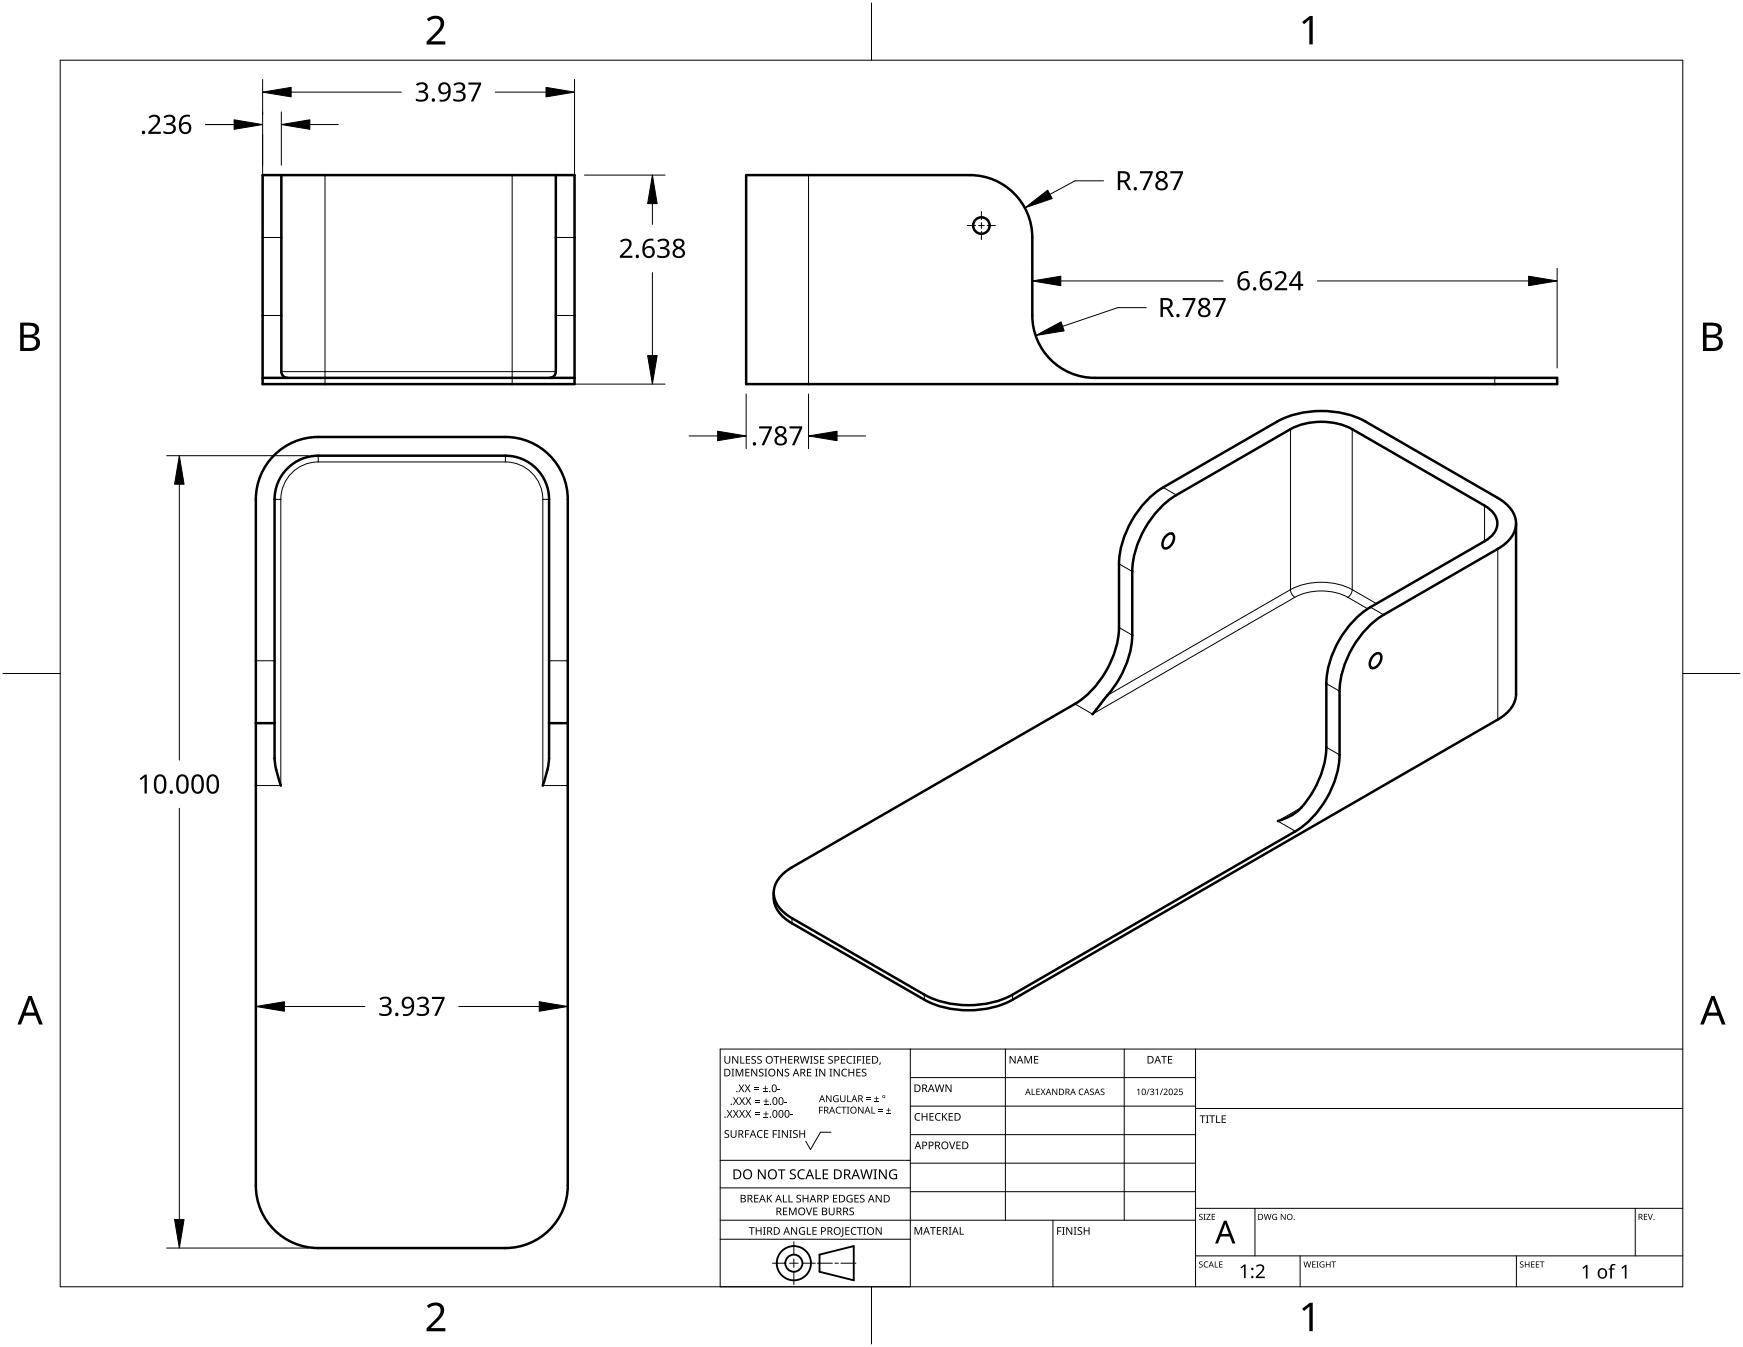
[picture p143: page 1]
