JHuinapi/Proyecto-biodise-o-13/Documentacion/Entregables/Entregable N°9/built/Dibujo polea circulo.pdf

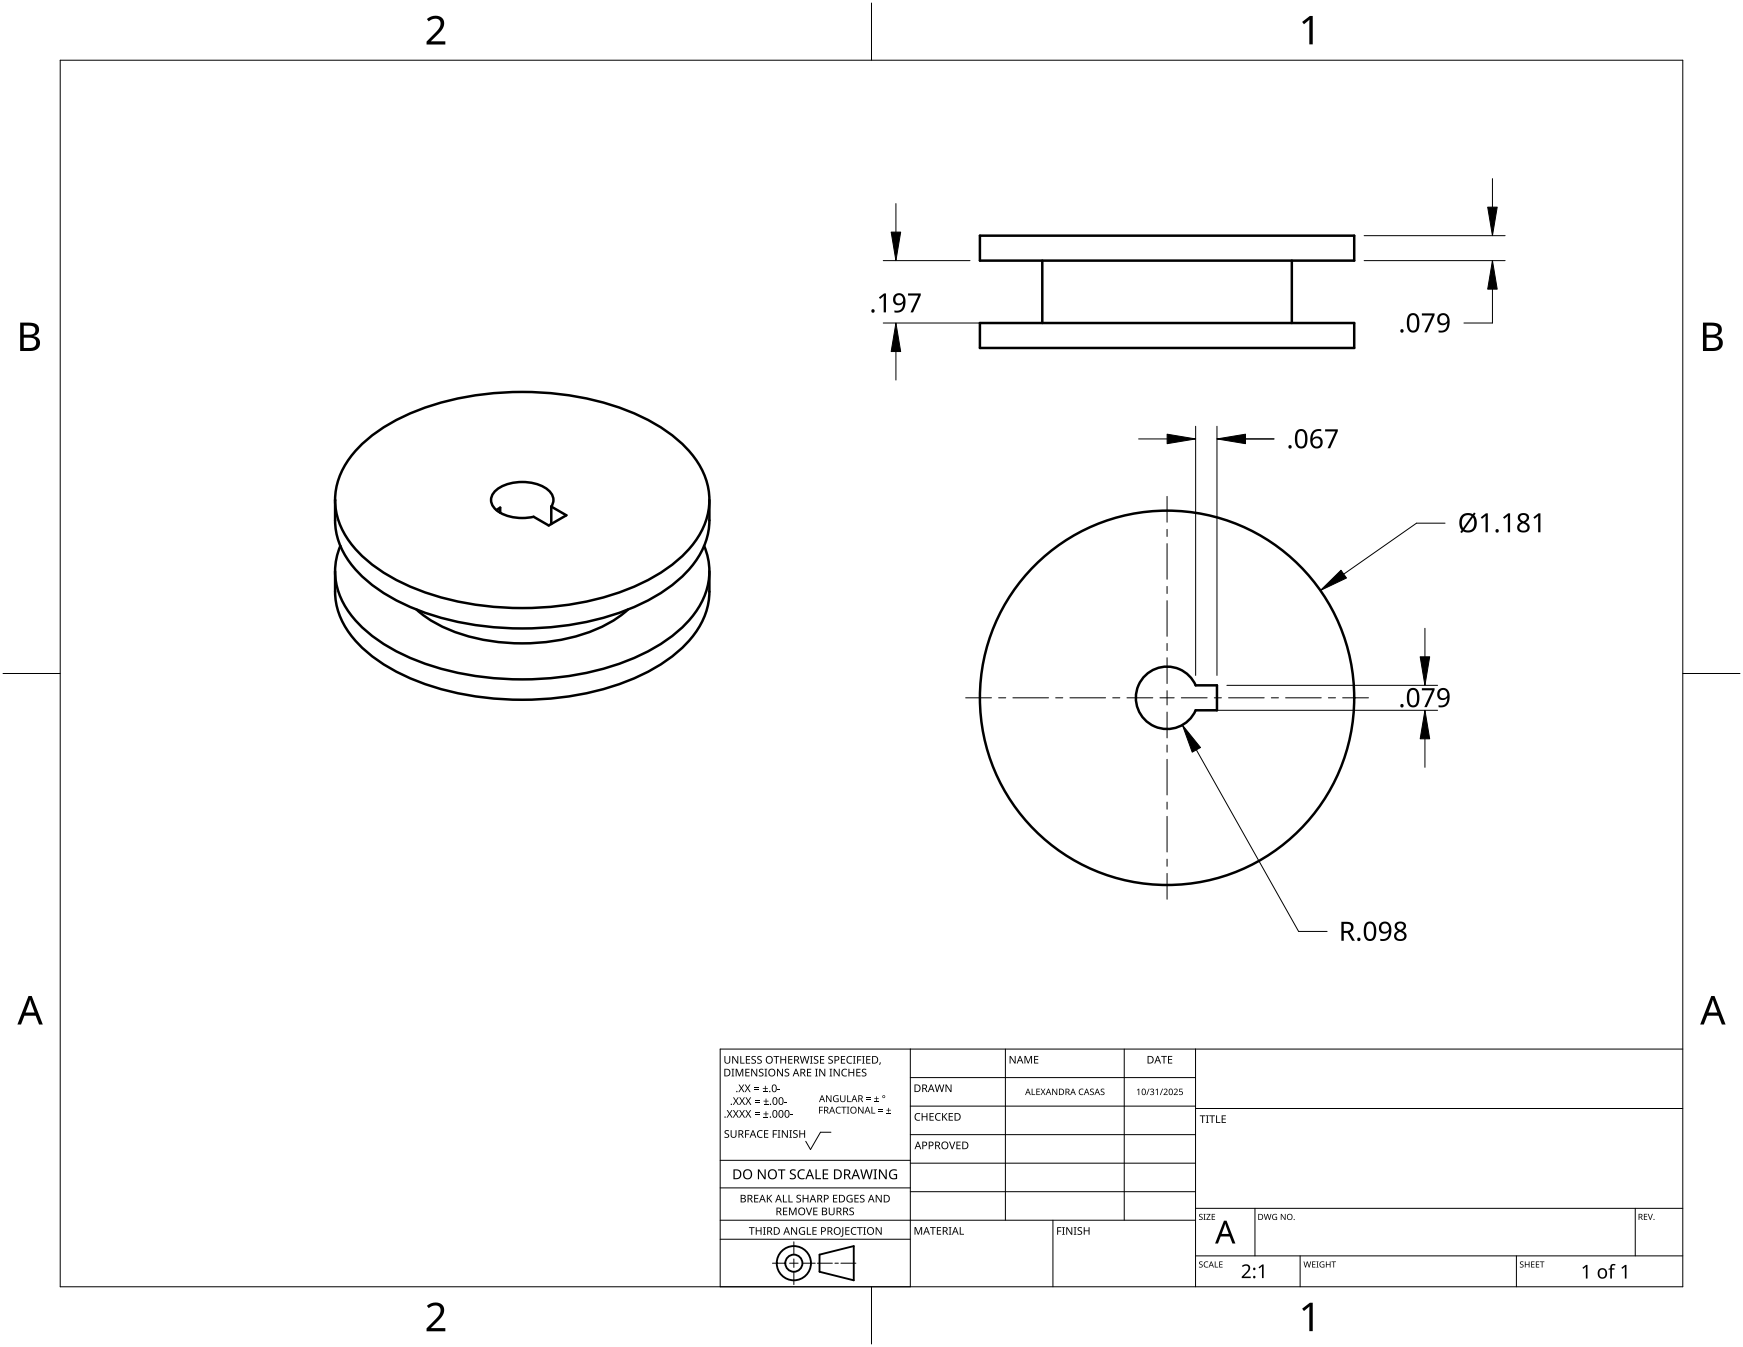
[picture p144: page 1]
