JHuinapi/Proyecto-biodise-o-13/Documentacion/Entregables/Entregable N°9/built/Dibujo rodilla 2.pdf

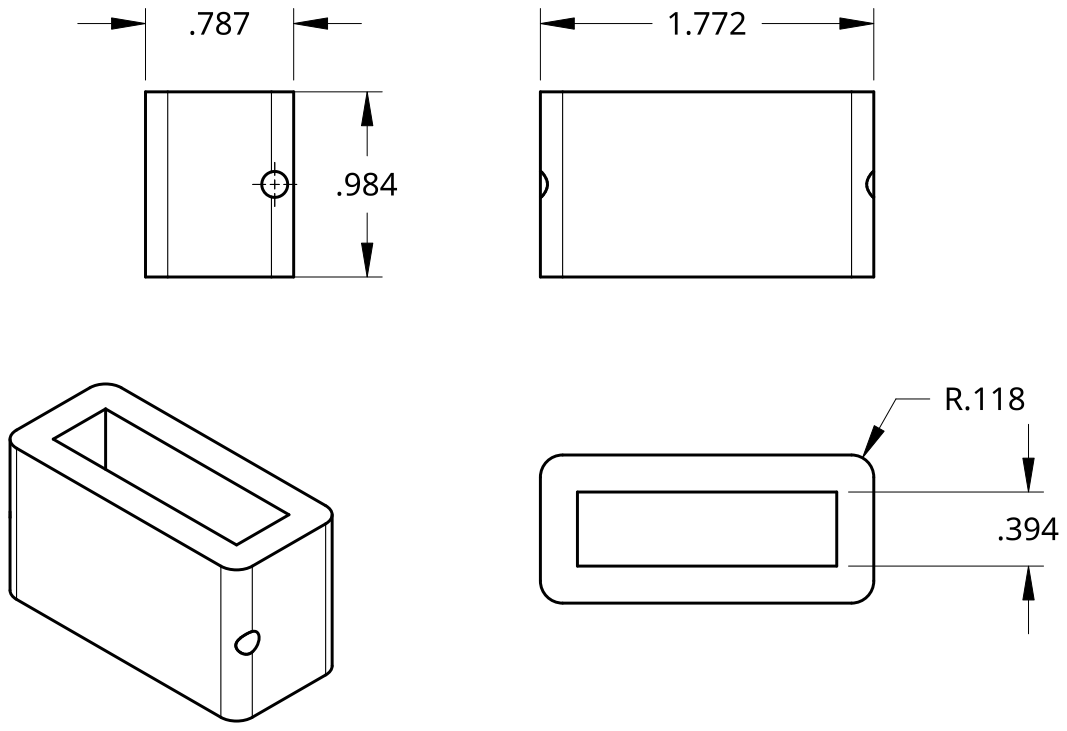
[picture p145: page 1]
